bei22002-cpu/pocketvault-d14/blueprints/assets/A1-lightline-mg-blueprint.png

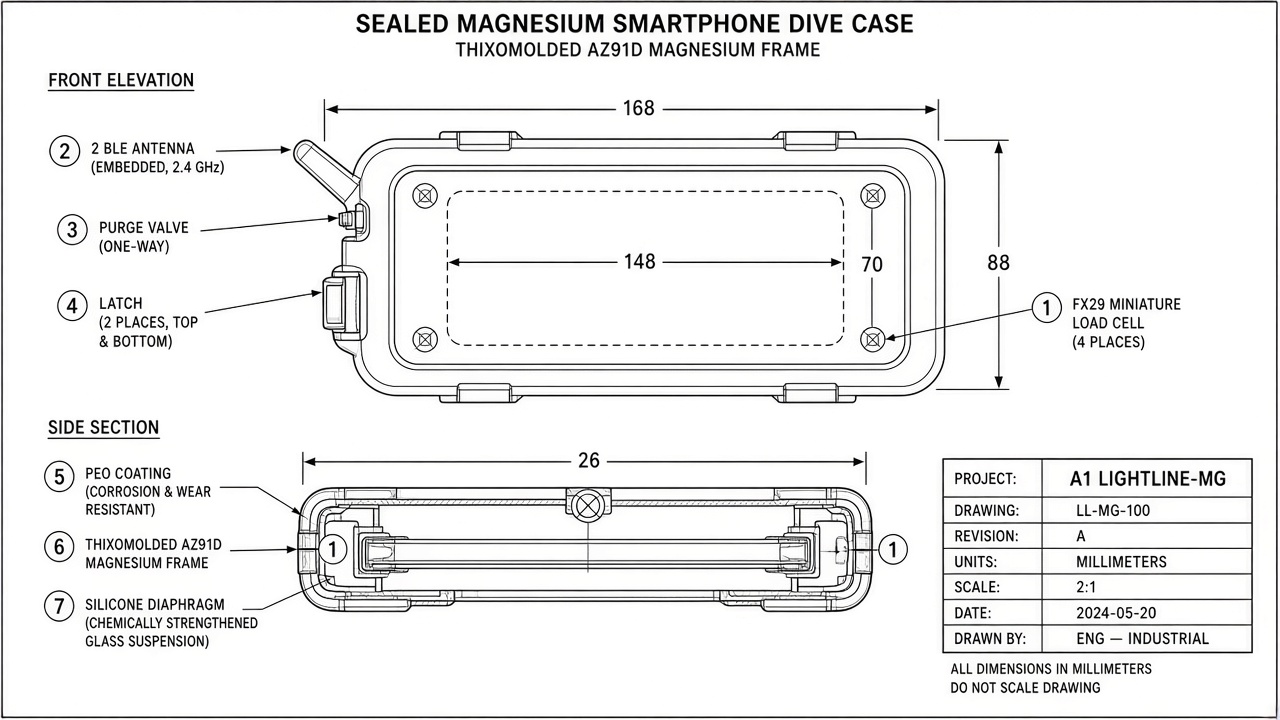
blueprints/assets/A1-lightline-mg-blueprint.png
