bei22002-cpu/pocketvault-d14/blueprints/assets/A2-carbonshell-blueprint.png

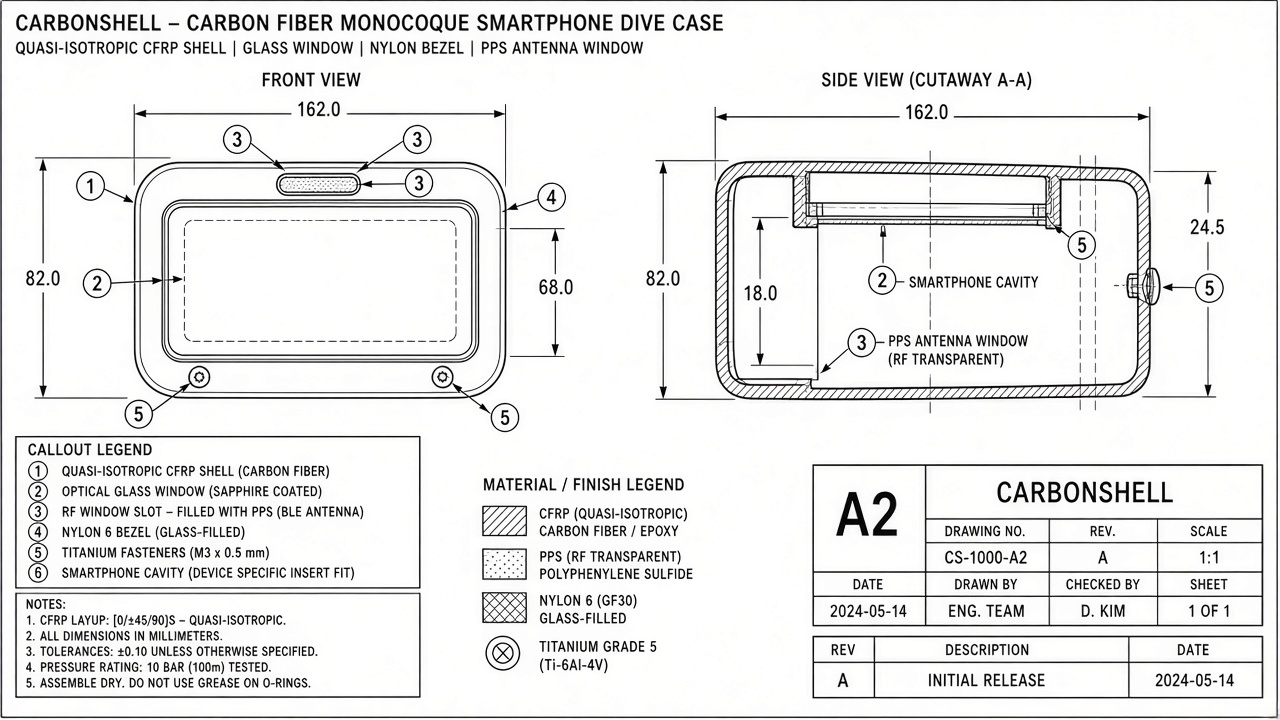
blueprints/assets/A2-carbonshell-blueprint.png
