bei22002-cpu/pocketvault-d14/blueprints/assets/A3-skeleton-blueprint.png

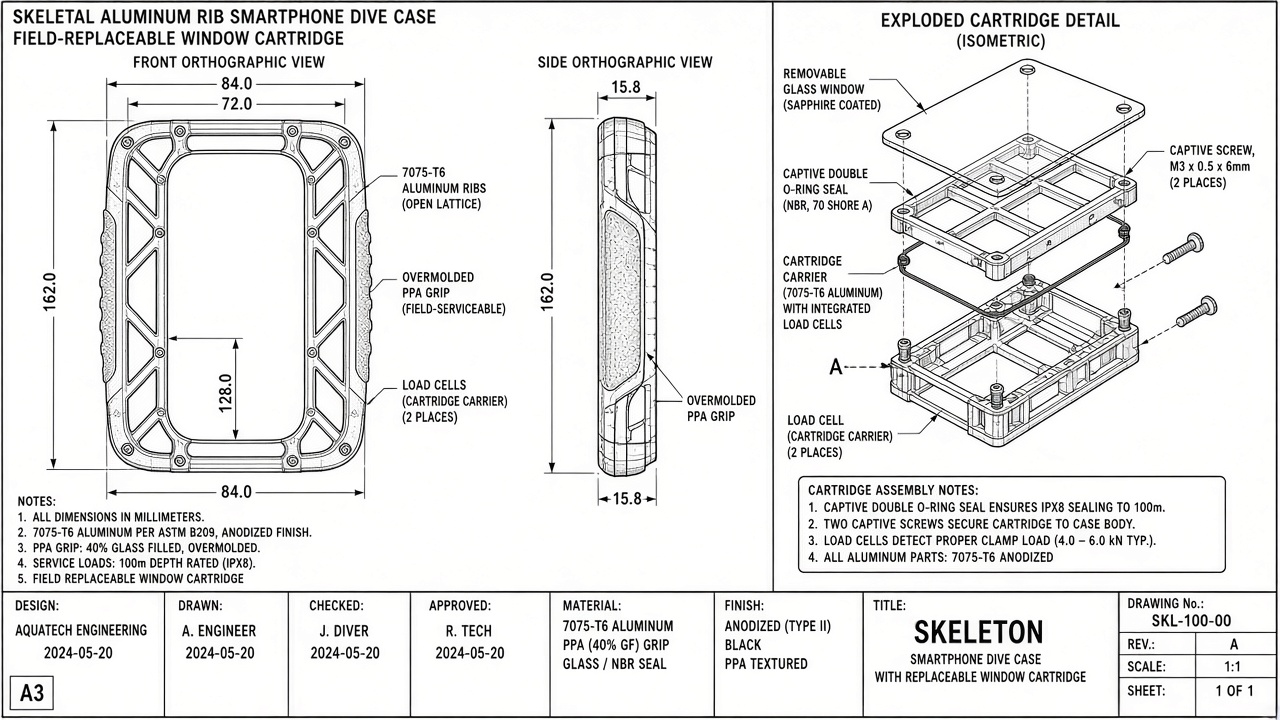
blueprints/assets/A3-skeleton-blueprint.png
