bei22002-cpu/pocketvault-d14/blueprints/assets/B5-hall-glove-blueprint.png

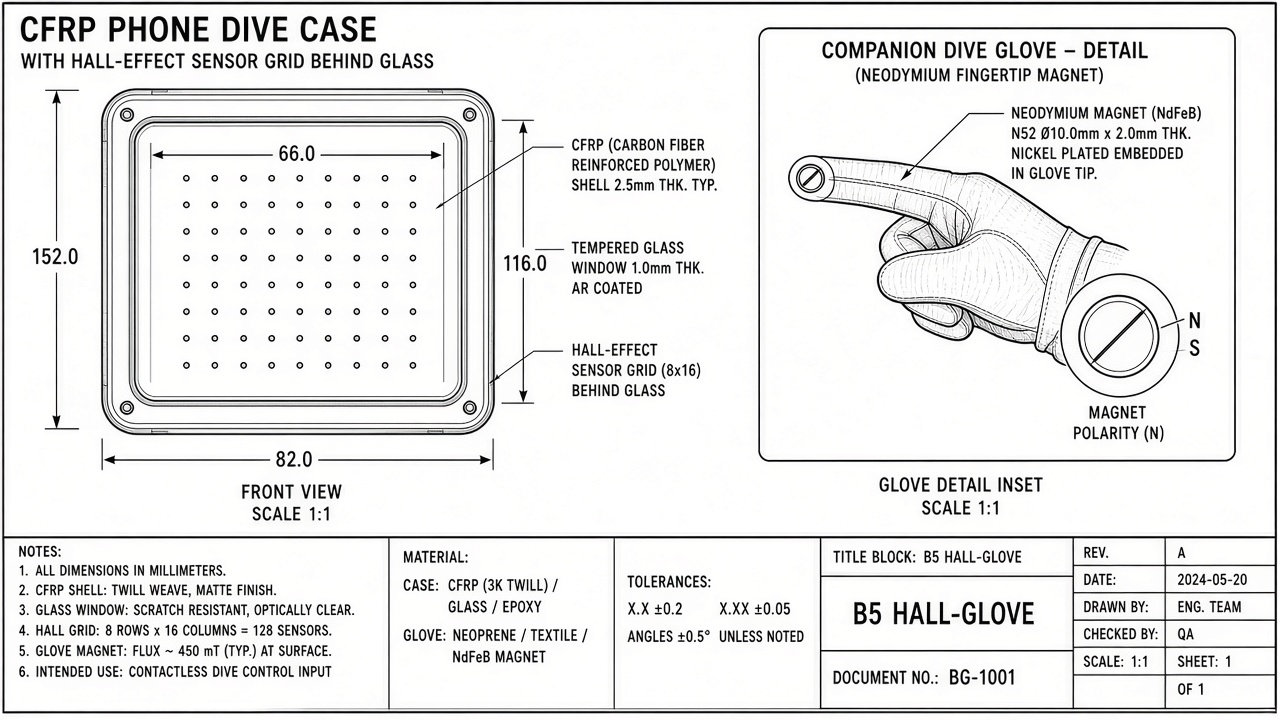
blueprints/assets/B5-hall-glove-blueprint.png
