bei22002-cpu/pocketvault-d14/blueprints/assets/B7-lamb-wave-blueprint.png

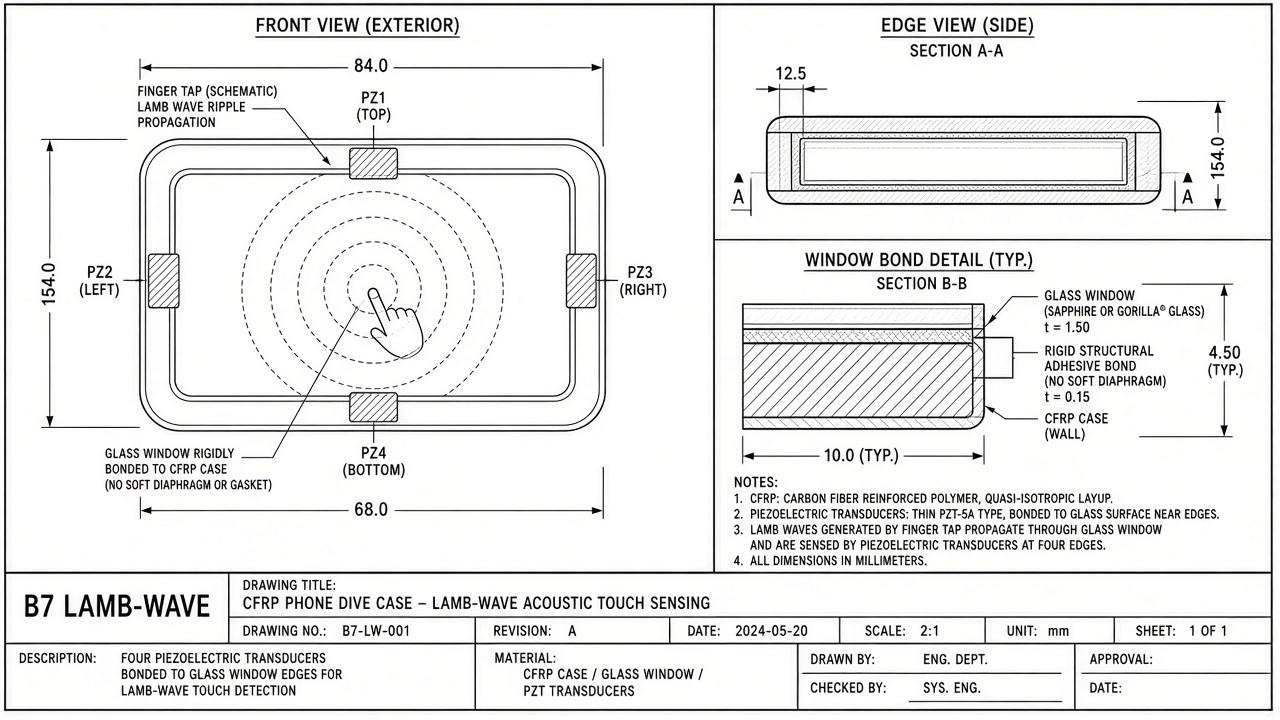
blueprints/assets/B7-lamb-wave-blueprint.png
