bei22002-cpu/pocketvault-d14/blueprints/assets/B8-resistive-hard-blueprint.png

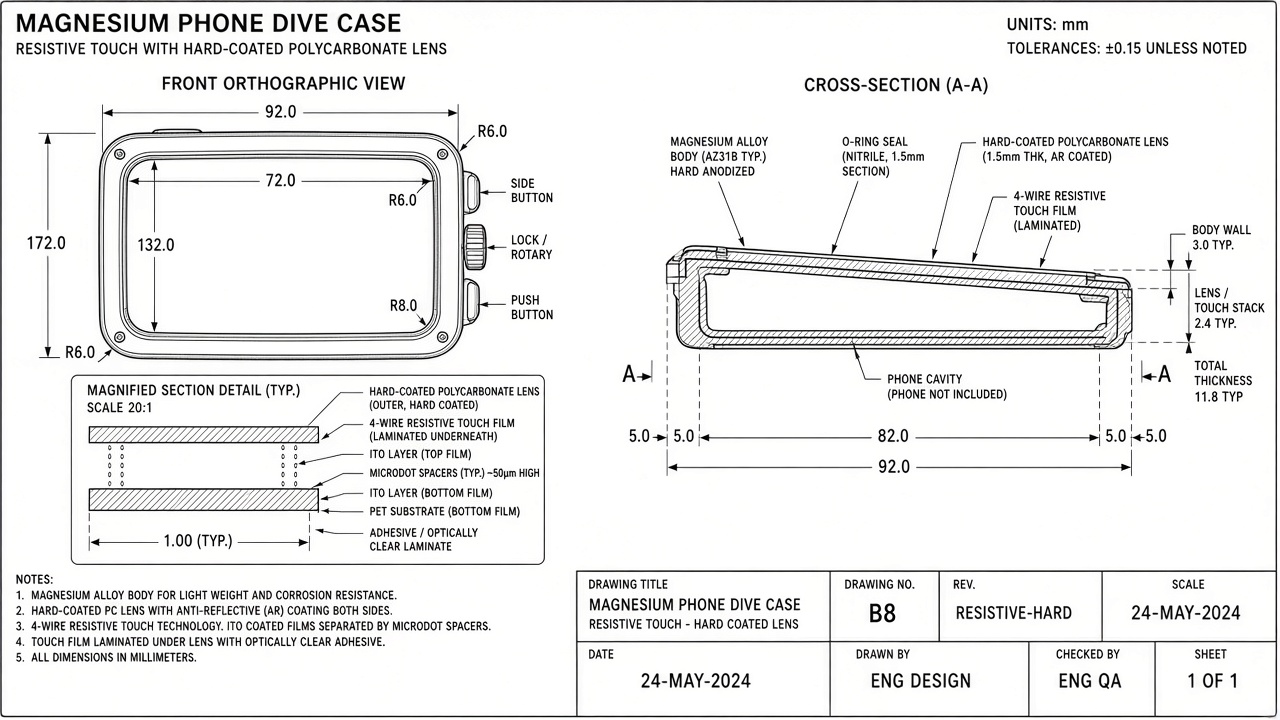
blueprints/assets/B8-resistive-hard-blueprint.png
