bei22002-cpu/pocketvault-d14/blueprints/assets/B9-gap-cap-blueprint.png

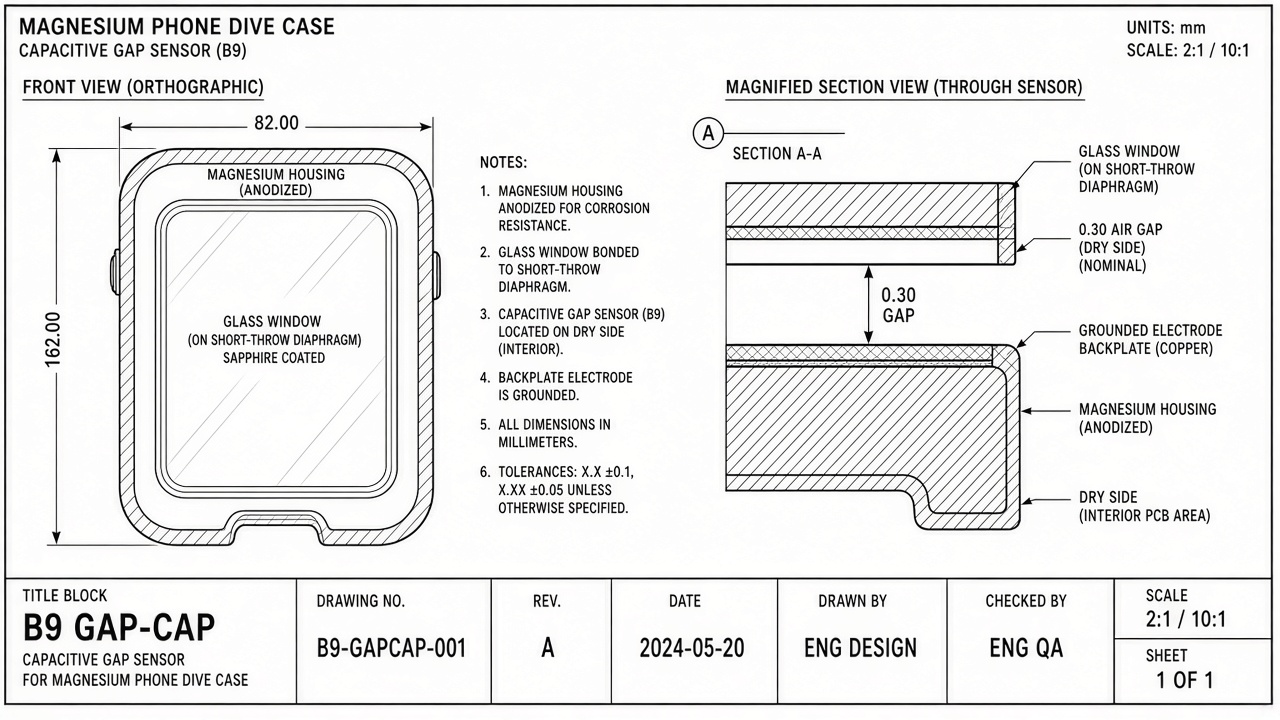
blueprints/assets/B9-gap-cap-blueprint.png
