bei22002-cpu/pocketvault-d14/blueprints/assets/C10-crownpad-blueprint.png

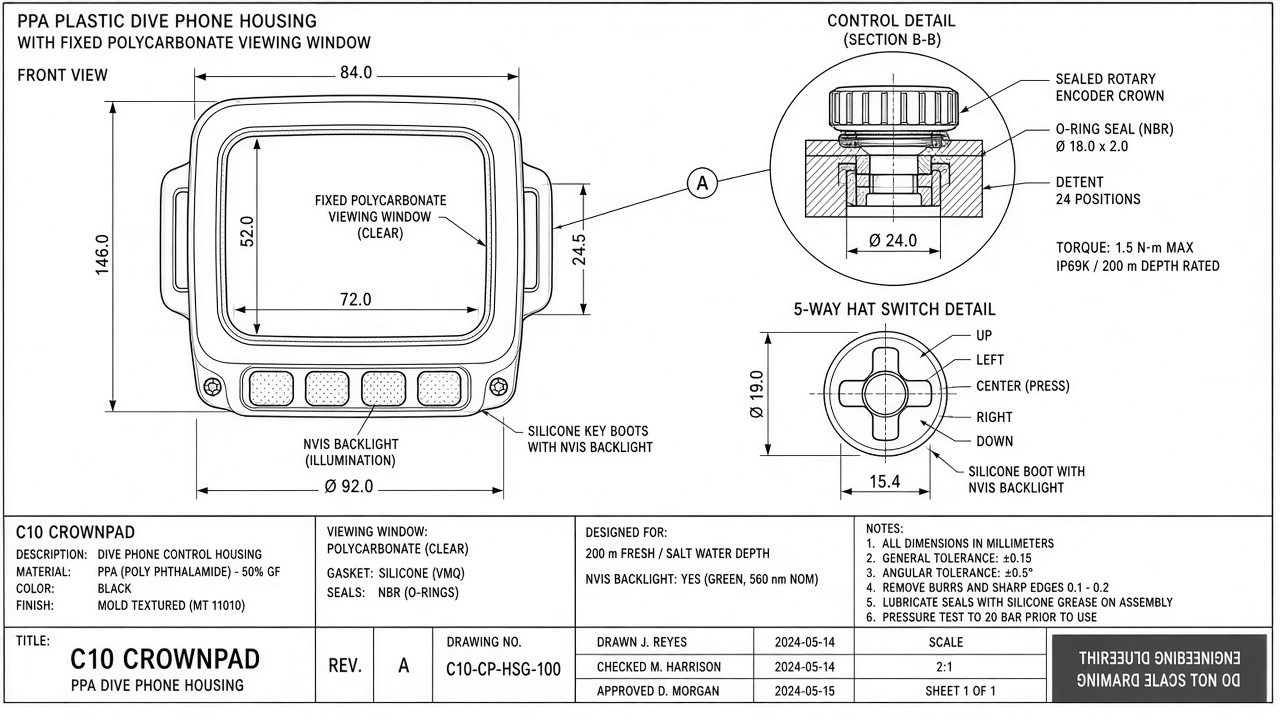
blueprints/assets/C10-crownpad-blueprint.png
