bei22002-cpu/pocketvault-d14/blueprints/assets/C11-tether-puck-blueprint.png

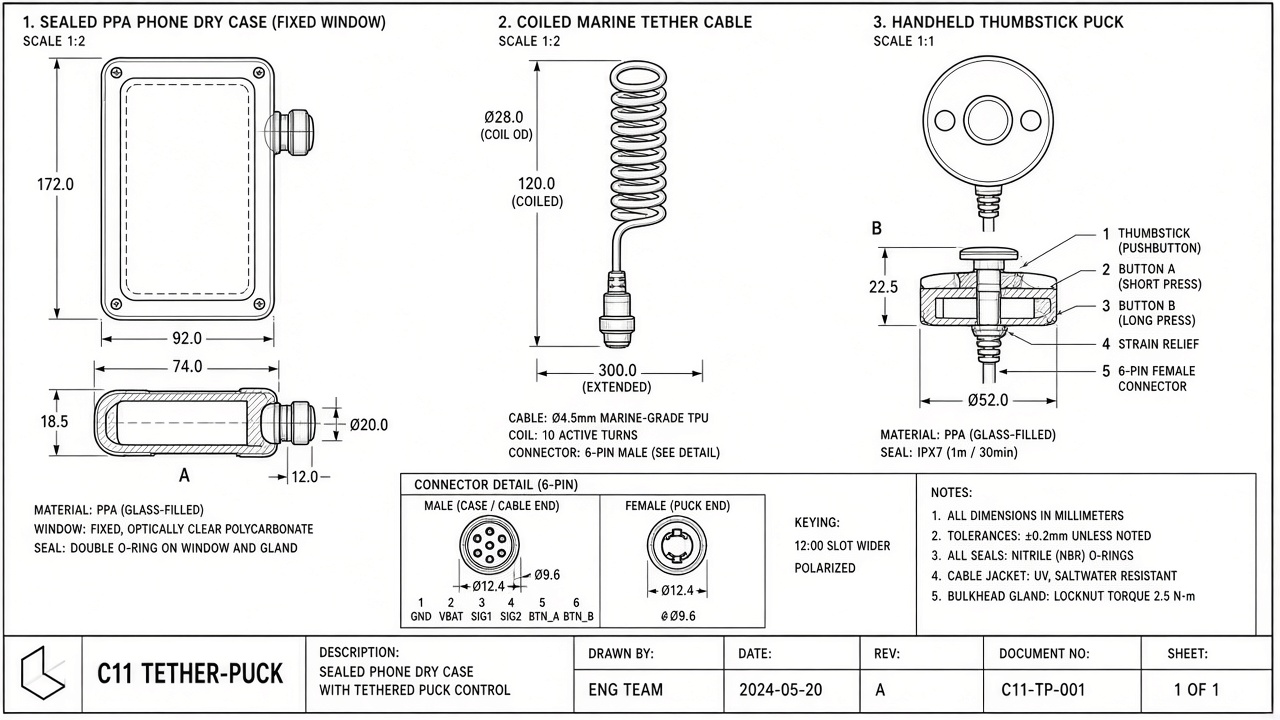
blueprints/assets/C11-tether-puck-blueprint.png
