bei22002-cpu/pocketvault-d14/blueprints/assets/C12-tilt-cursor-blueprint.png

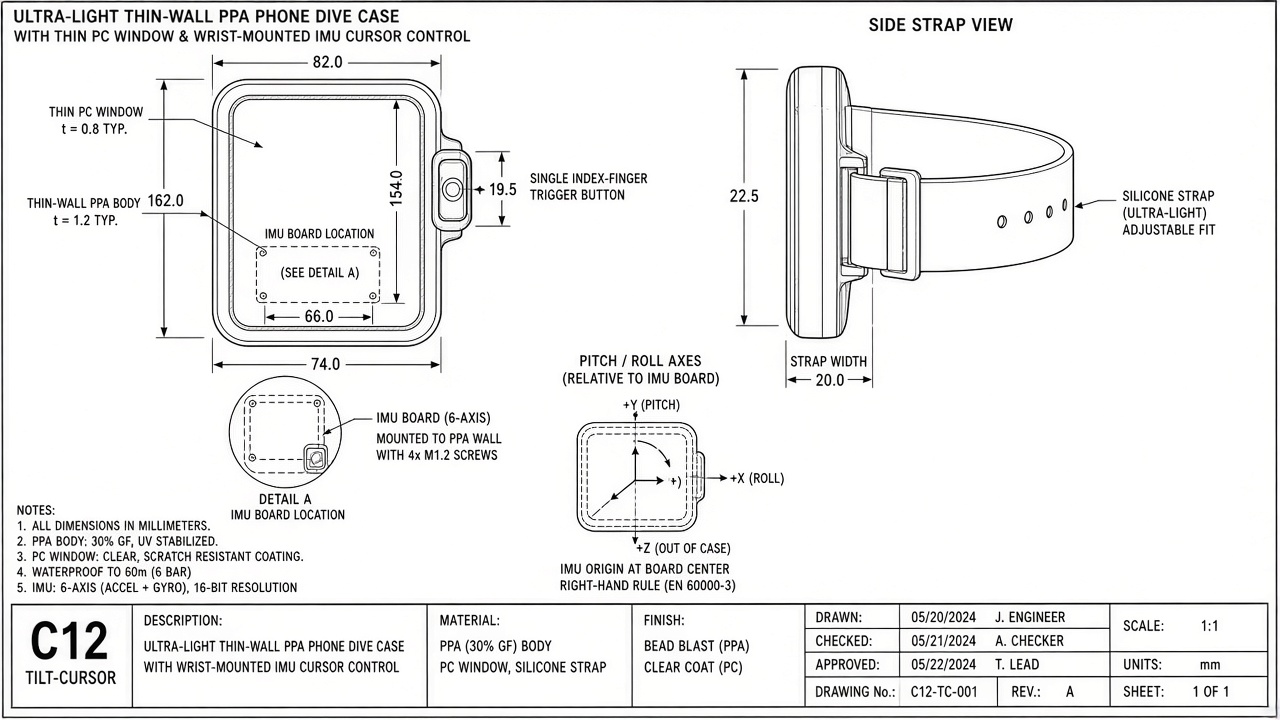
blueprints/assets/C12-tilt-cursor-blueprint.png
