bei22002-cpu/pocketvault-d14/blueprints/assets/D14-rolltop-blueprint.png

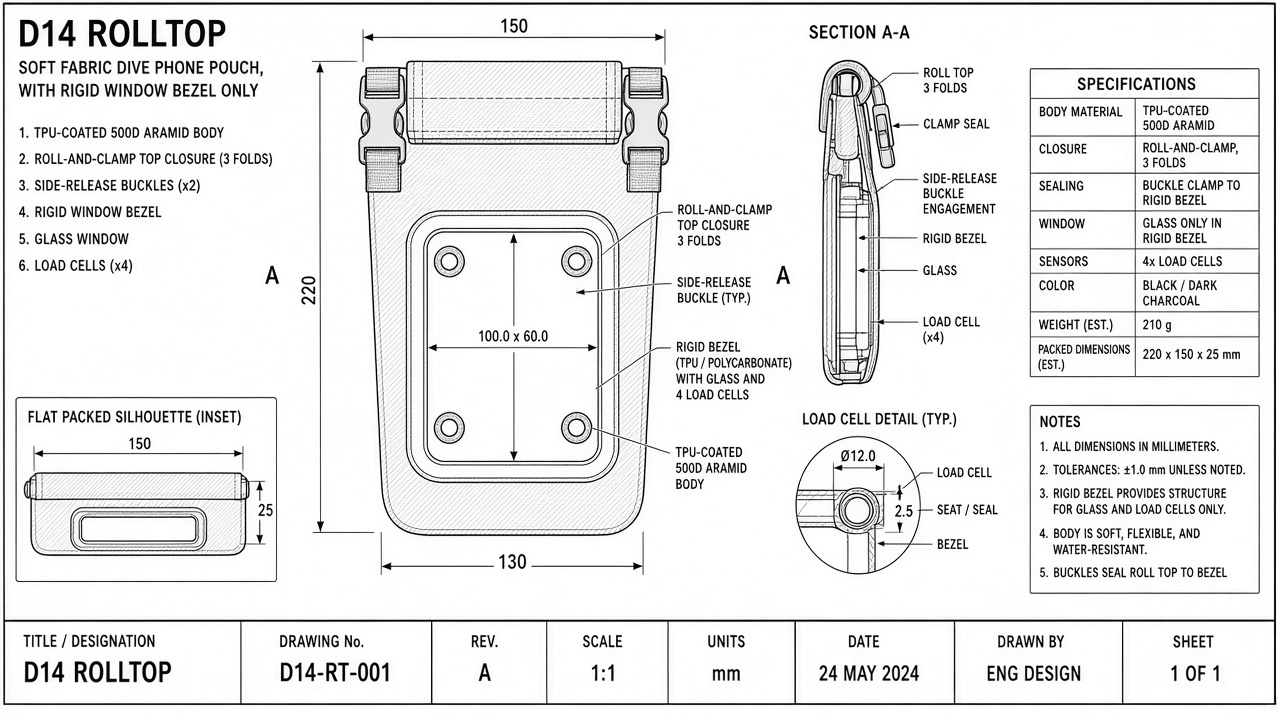
blueprints/assets/D14-rolltop-blueprint.png
