bei22002-cpu/pocketvault-d14/blueprints/assets/D15-oilfill-100-blueprint.png

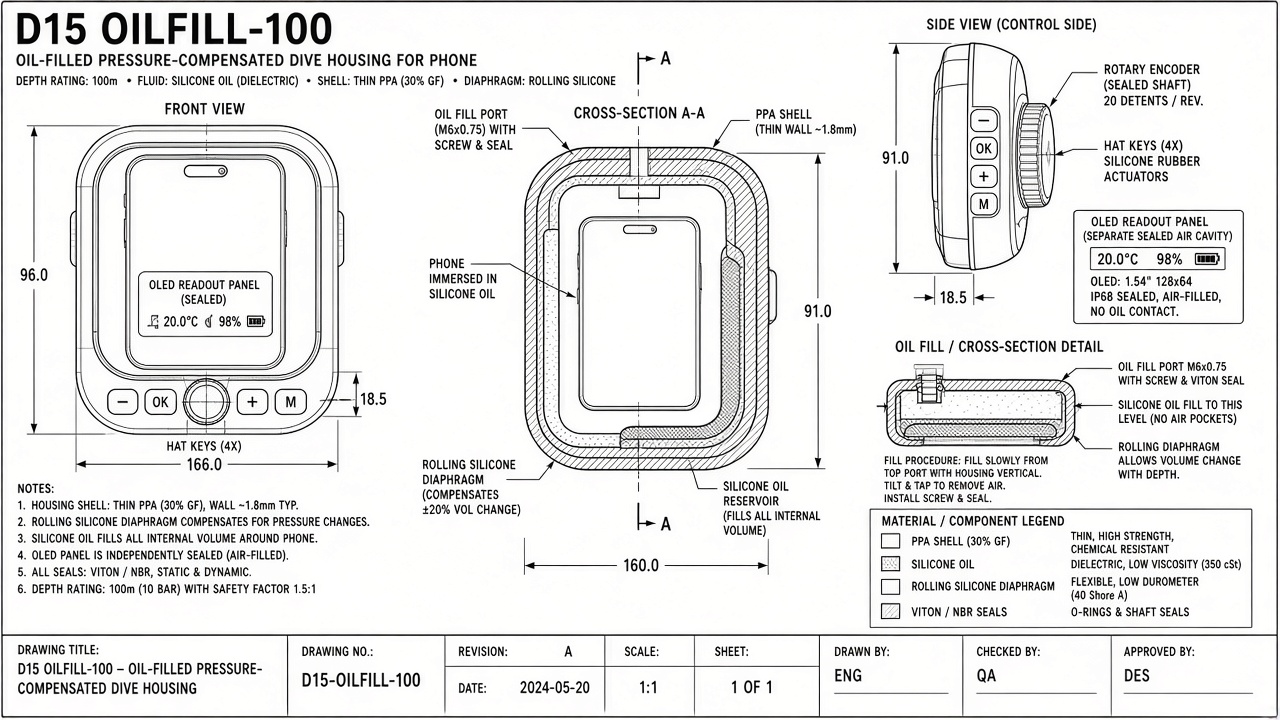
blueprints/assets/D15-oilfill-100-blueprint.png
