bei22002-cpu/pocketvault-d14/blueprints/assets/D16-floatline-blueprint.png

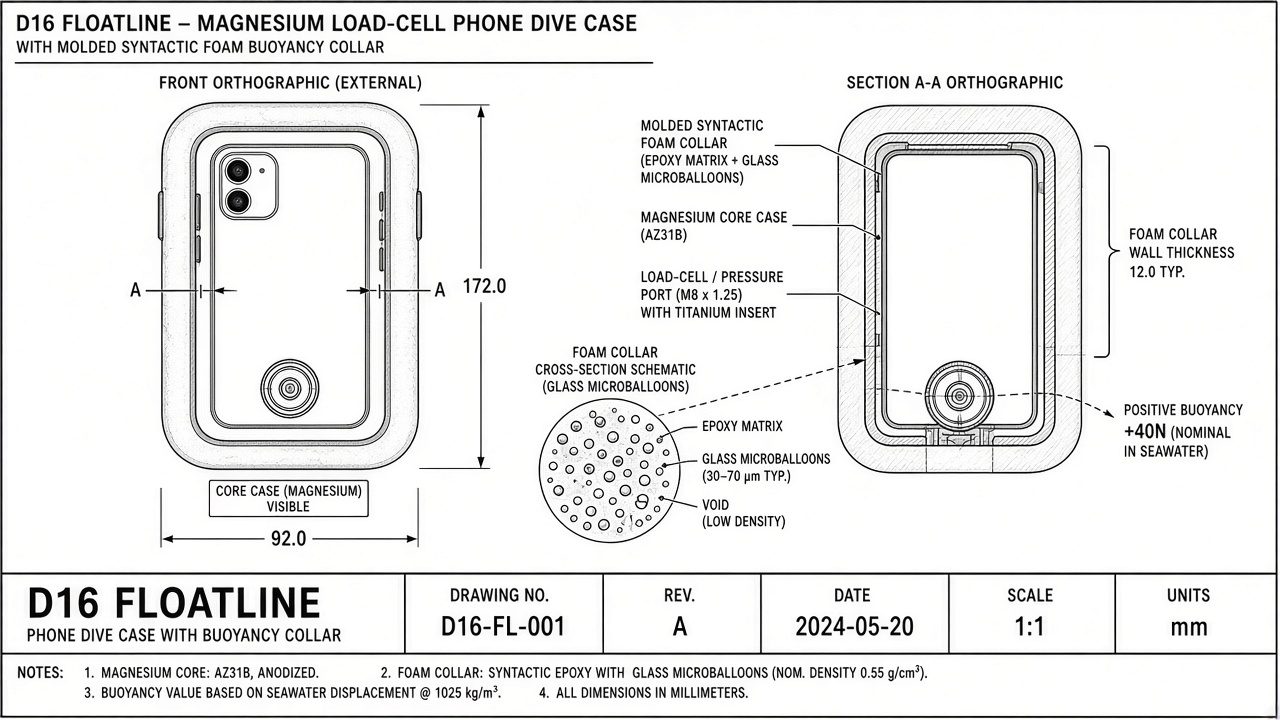
blueprints/assets/D16-floatline-blueprint.png
