bei22002-cpu/pocketvault-d14/blueprints/assets/D17-chestboard-blueprint.png

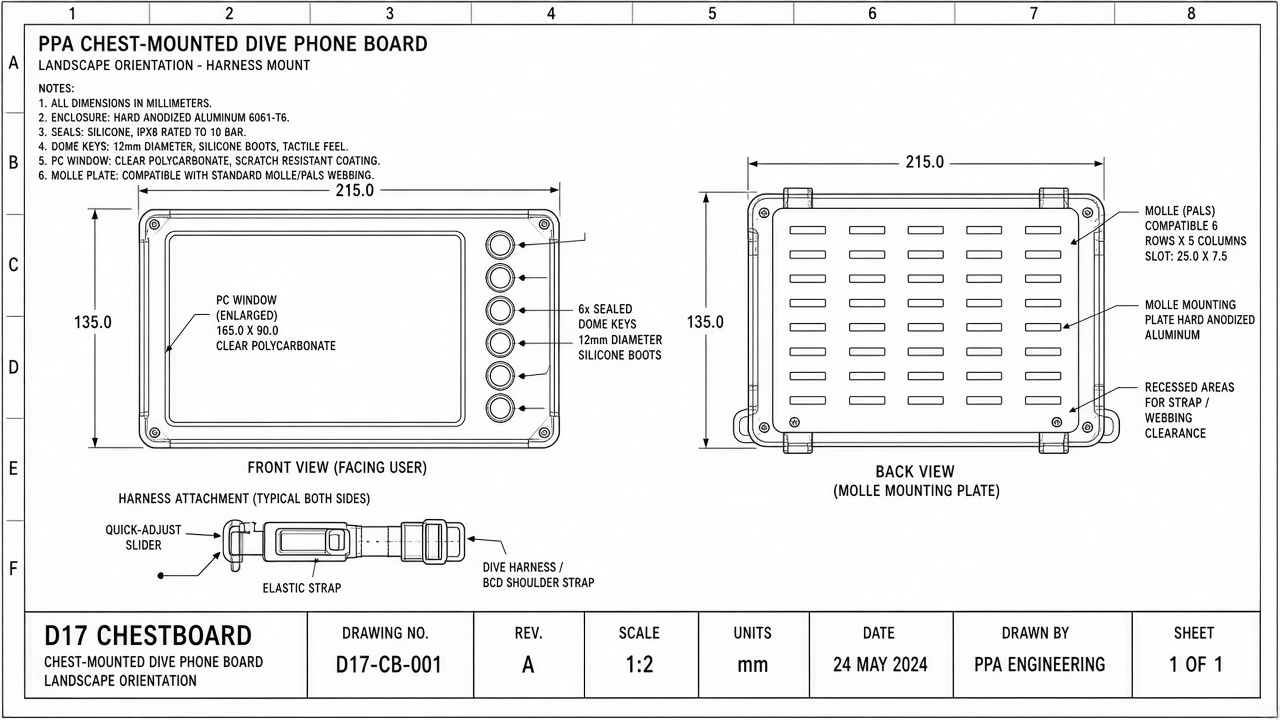
blueprints/assets/D17-chestboard-blueprint.png
