bei22002-cpu/pocketvault-d14/blueprints/assets/D18-gauntlet-blueprint.png

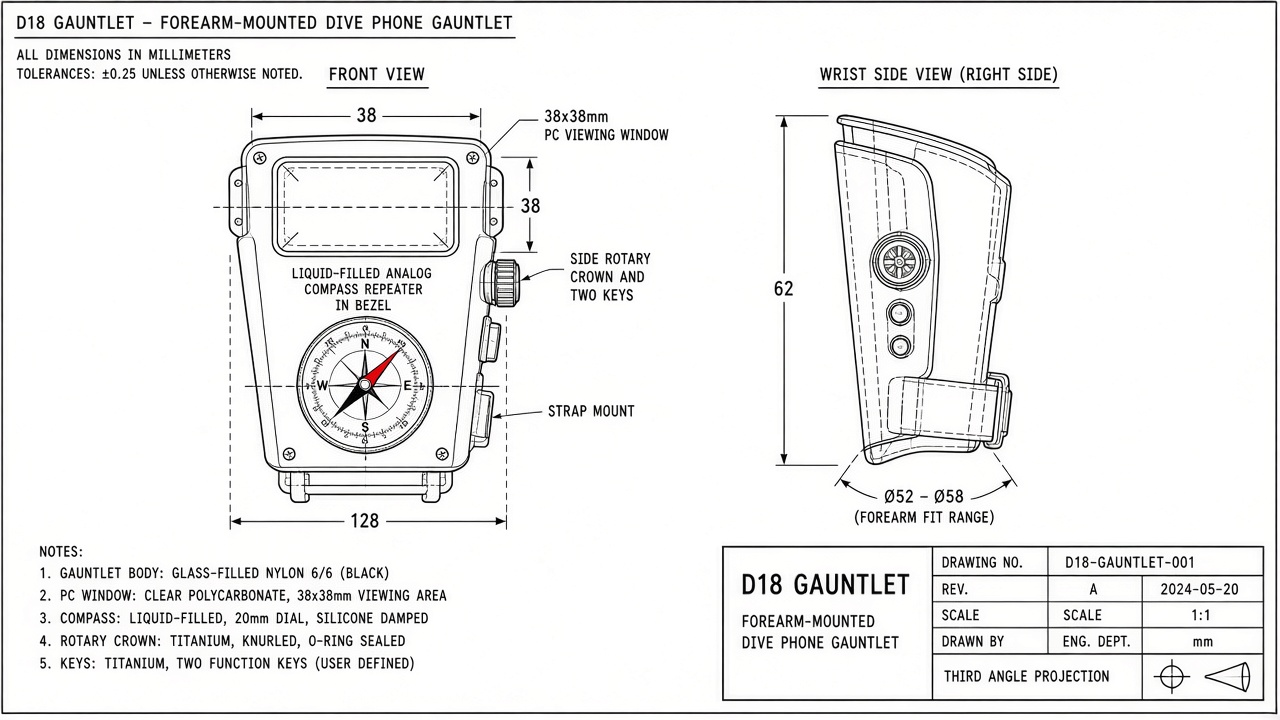
blueprints/assets/D18-gauntlet-blueprint.png
