bei22002-cpu/pocketvault-d14/blueprints/hq/hq-A2-work.png

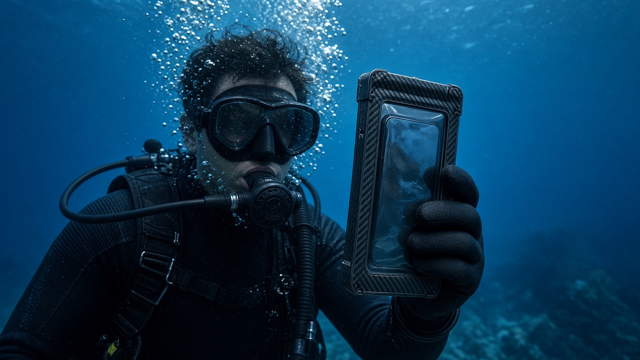
blueprints/hq/hq-A2-work.png
