bei22002-cpu/pocketvault-d14/blueprints/hq/hq-A3-explode.png

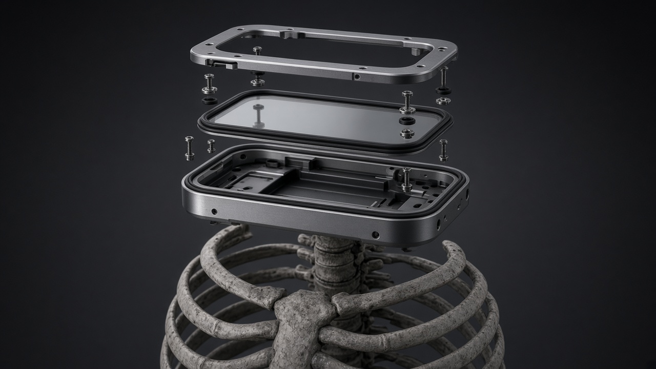
blueprints/hq/hq-A3-explode.png
