bei22002-cpu/pocketvault-d14/blueprints/hq/hq-B5-explode.png

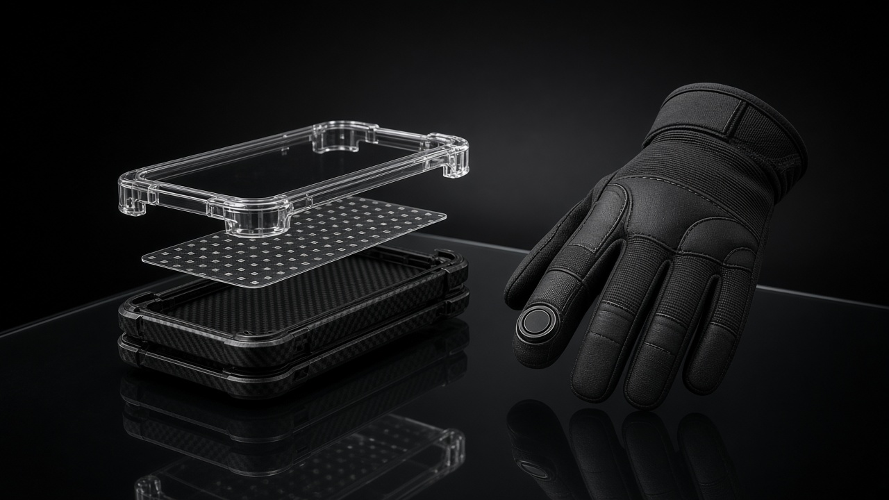
blueprints/hq/hq-B5-explode.png
