bei22002-cpu/pocketvault-d14/blueprints/hq/hq-B6-explode.png

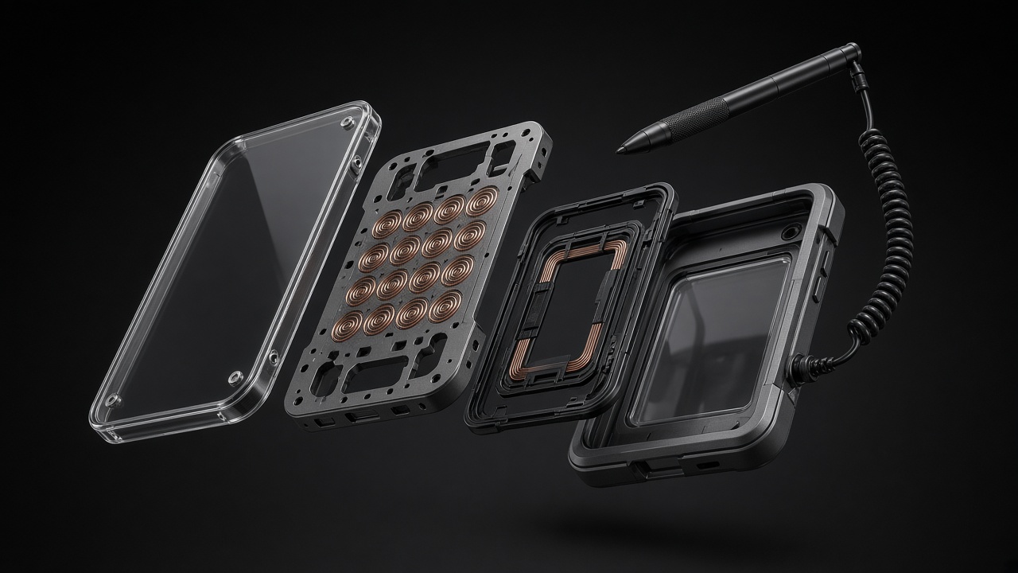
blueprints/hq/hq-B6-explode.png
