bei22002-cpu/pocketvault-d14/blueprints/hq/hq-B7-explode.png

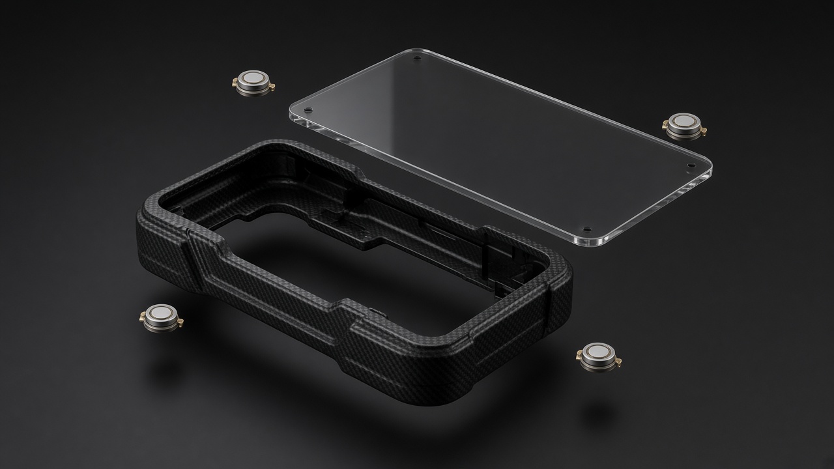
blueprints/hq/hq-B7-explode.png
