bei22002-cpu/pocketvault-d14/blueprints/hq/hq-B8-work.png

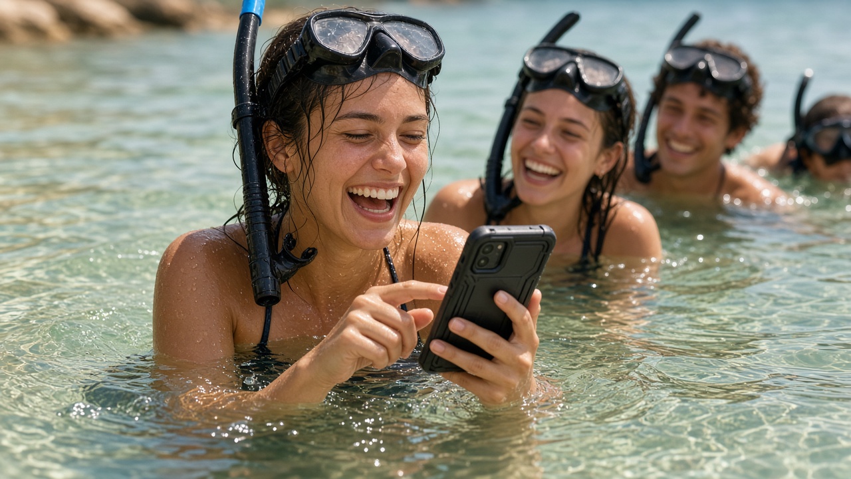
blueprints/hq/hq-B8-work.png
