bei22002-cpu/pocketvault-d14/blueprints/hq/hq-C10-work.png

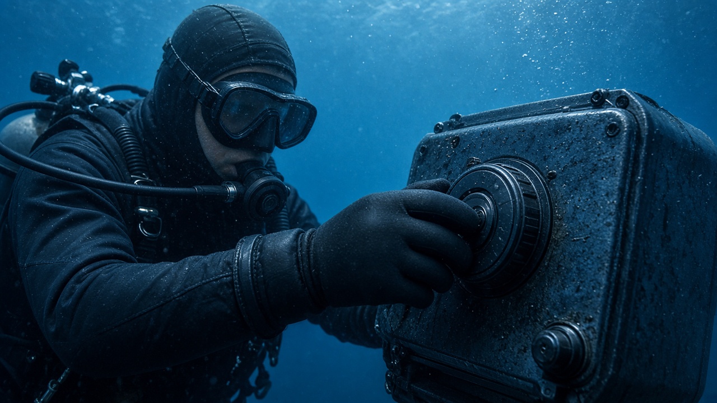
blueprints/hq/hq-C10-work.png
