bei22002-cpu/pocketvault-d14/blueprints/hq/hq-C11-explode.png

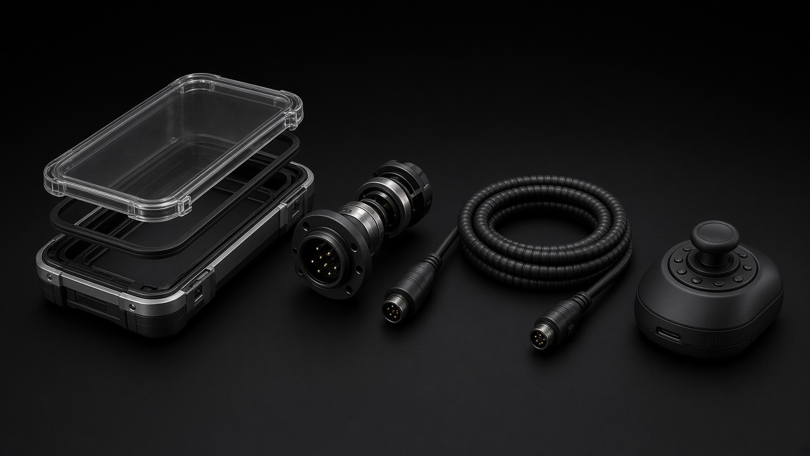
blueprints/hq/hq-C11-explode.png
