bei22002-cpu/pocketvault-d14/blueprints/hq/hq-C12-explode.png

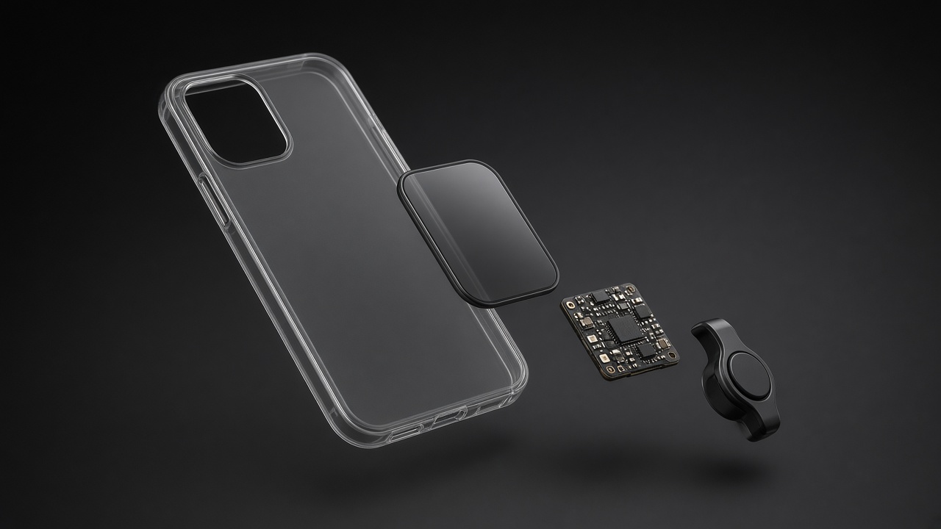
blueprints/hq/hq-C12-explode.png
