bei22002-cpu/pocketvault-d14/blueprints/hq/hq-C13-work.png

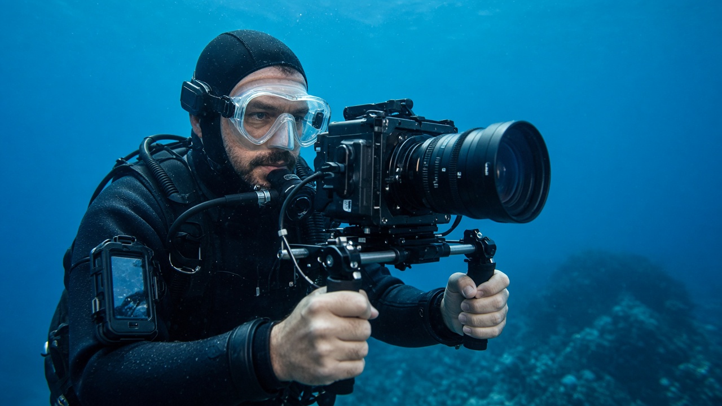
blueprints/hq/hq-C13-work.png
