bei22002-cpu/pocketvault-d14/blueprints/hq/hq-D14-explode.png

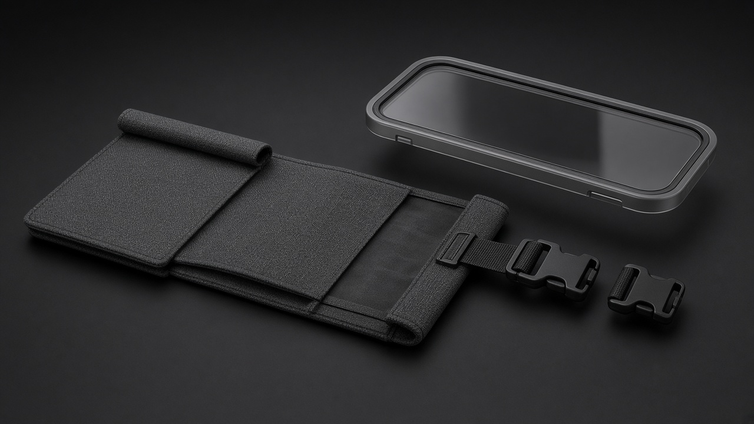
blueprints/hq/hq-D14-explode.png
