bei22002-cpu/pocketvault-d14/blueprints/hq/hq-D14-work.png

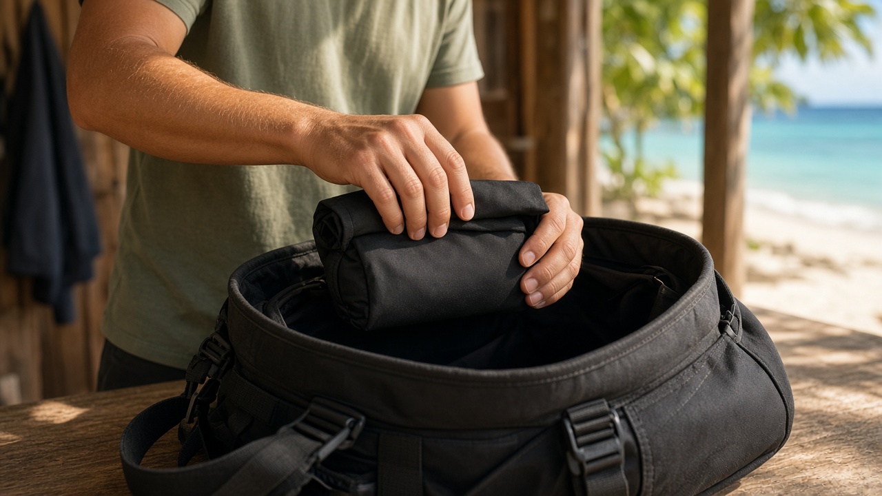
blueprints/hq/hq-D14-work.png
