bei22002-cpu/pocketvault-d14/blueprints/hq/hq-D15-explode.png

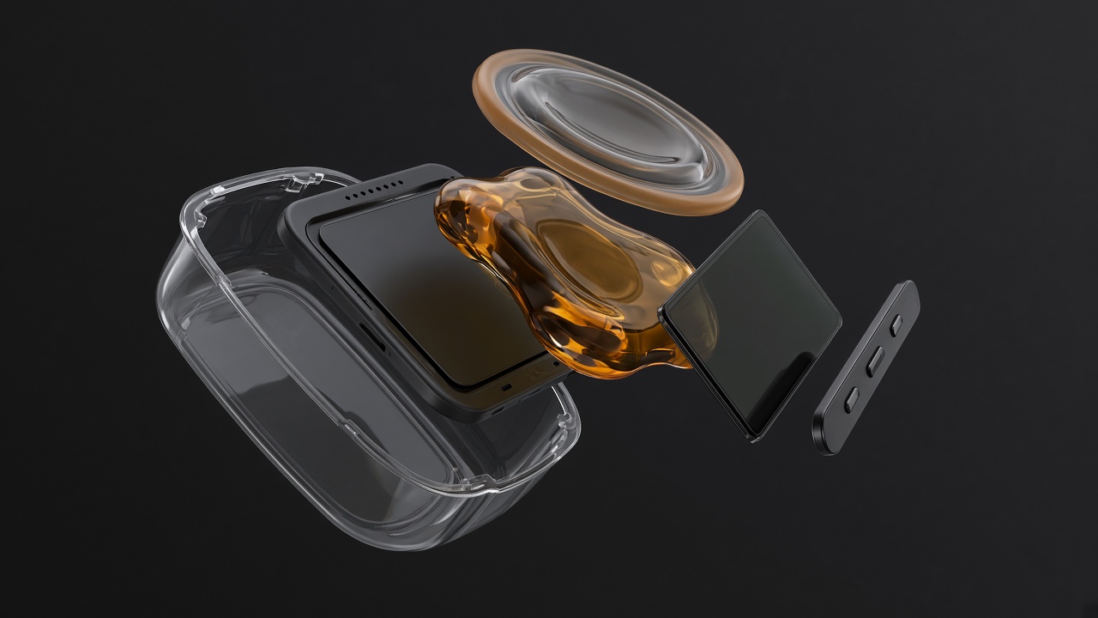
blueprints/hq/hq-D15-explode.png
