bei22002-cpu/pocketvault-d14/blueprints/hq/hq-D16-explode.png

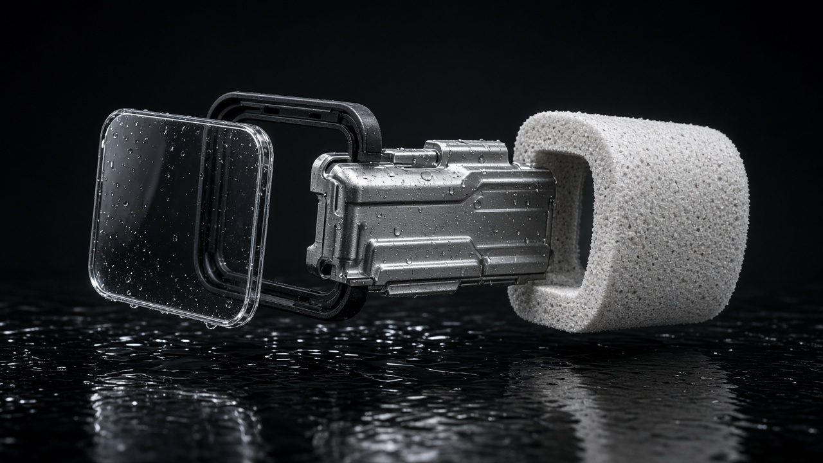
blueprints/hq/hq-D16-explode.png
