bei22002-cpu/pocketvault-d14/blueprints/hq/hq-D17-explode.png

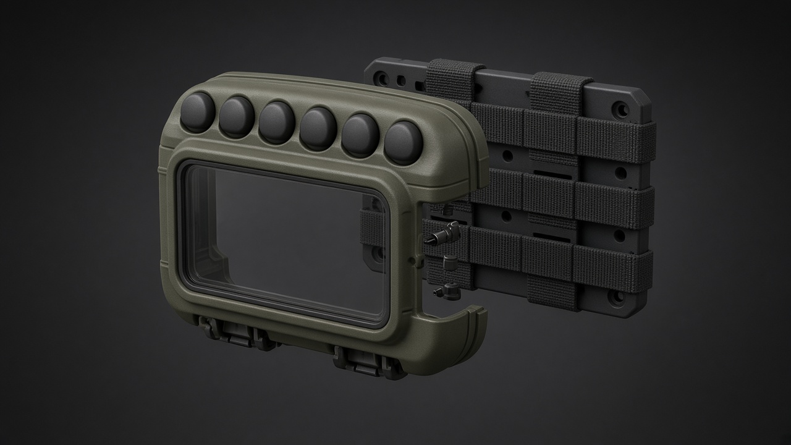
blueprints/hq/hq-D17-explode.png
