bei22002-cpu/pocketvault-d14/blueprints/hq/hq-D17-work.png

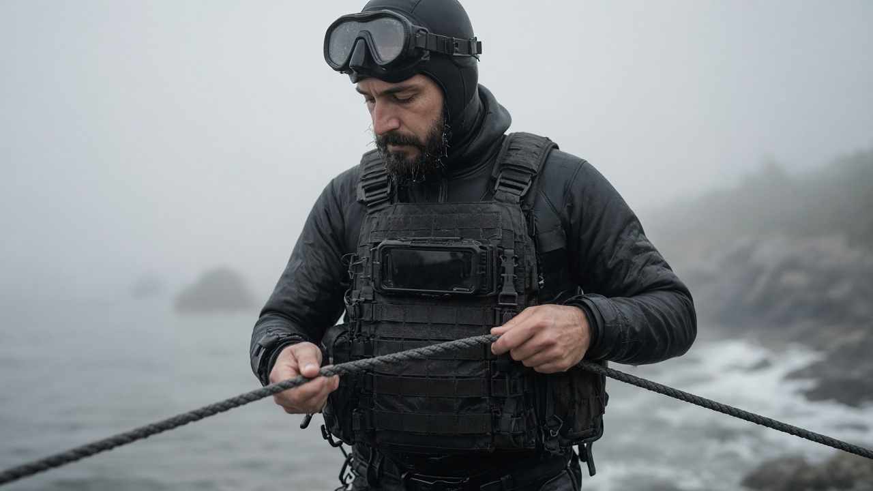
blueprints/hq/hq-D17-work.png
