bei22002-cpu/pocketvault-d14/blueprints/lifestyle/life-A1-lightline-mg.png

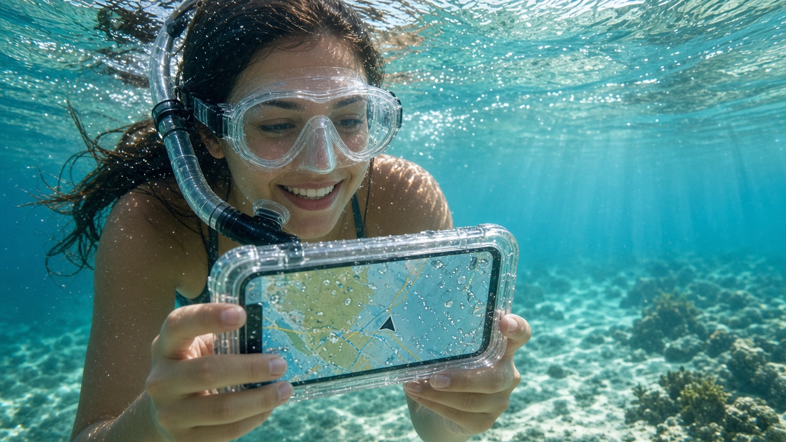
blueprints/lifestyle/life-A1-lightline-mg.png
