bei22002-cpu/pocketvault-d14/blueprints/lifestyle/life-A2-carbonshell.png

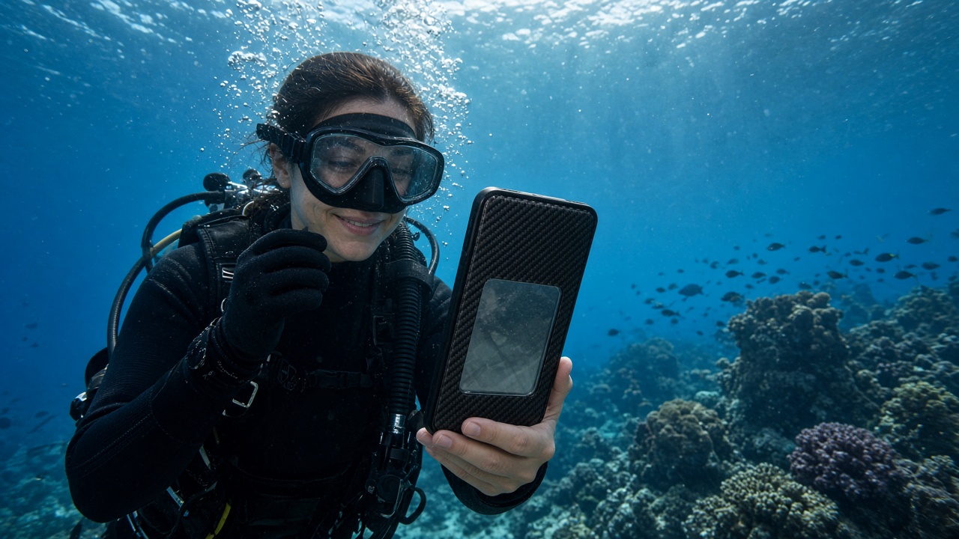
blueprints/lifestyle/life-A2-carbonshell.png
