bei22002-cpu/pocketvault-d14/blueprints/lifestyle/life-A3-skeleton.png

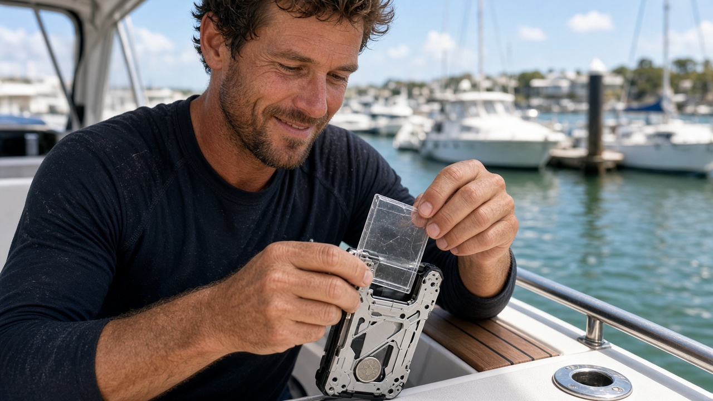
blueprints/lifestyle/life-A3-skeleton.png
