bei22002-cpu/pocketvault-d14/blueprints/lifestyle/life-A4-titan-20.png

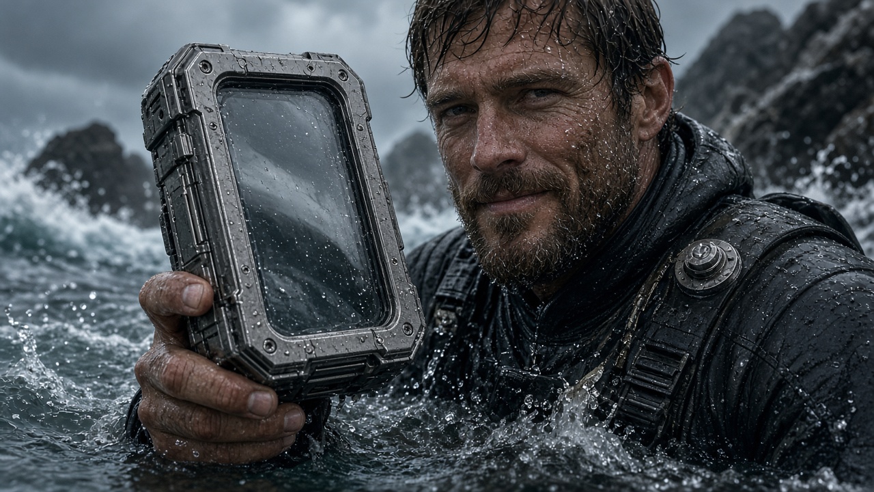
blueprints/lifestyle/life-A4-titan-20.png
