bei22002-cpu/pocketvault-d14/blueprints/lifestyle/life-B5-hall-glove.png

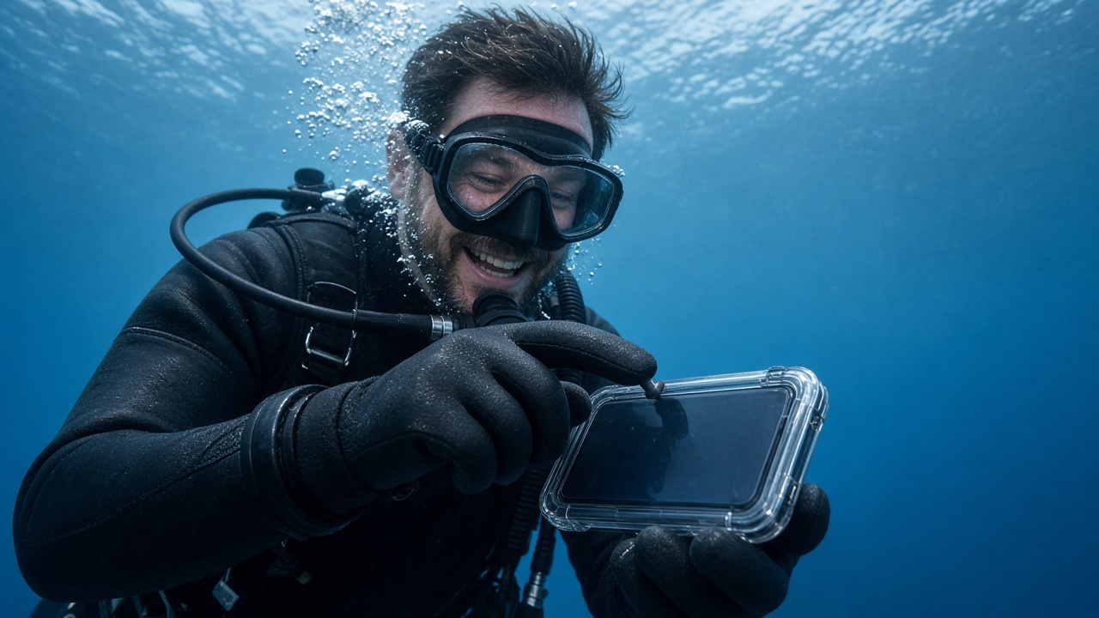
blueprints/lifestyle/life-B5-hall-glove.png
