bei22002-cpu/pocketvault-d14/blueprints/lifestyle/life-B6-stylus-emr.png

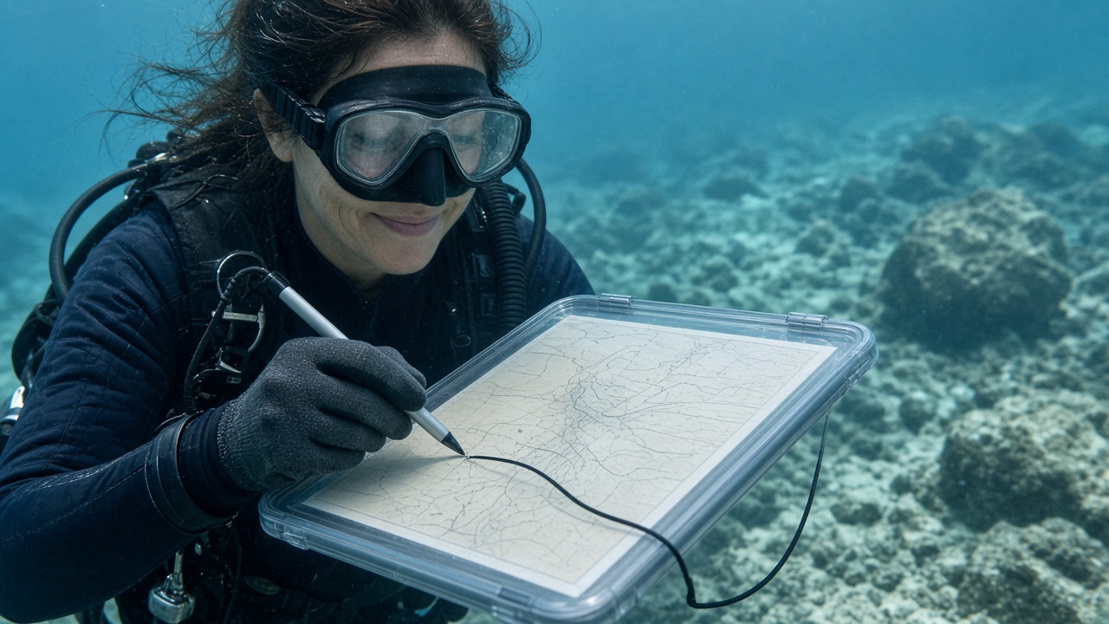
blueprints/lifestyle/life-B6-stylus-emr.png
