bei22002-cpu/pocketvault-d14/blueprints/lifestyle/life-B7-lamb-wave.png

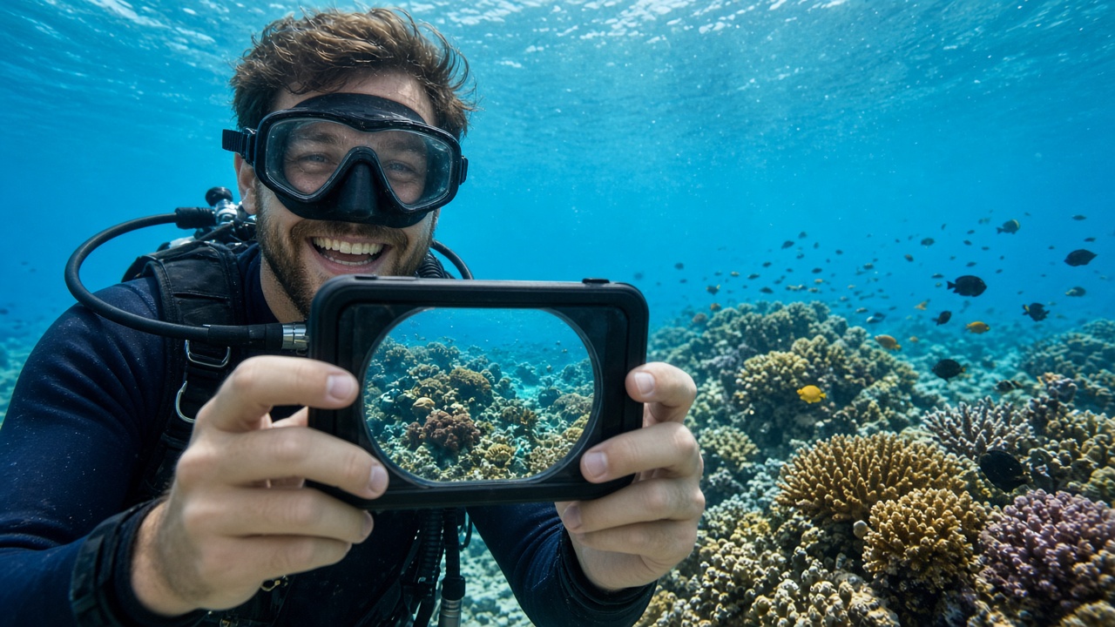
blueprints/lifestyle/life-B7-lamb-wave.png
