bei22002-cpu/pocketvault-d14/blueprints/lifestyle/life-B8-resistive-hard.png

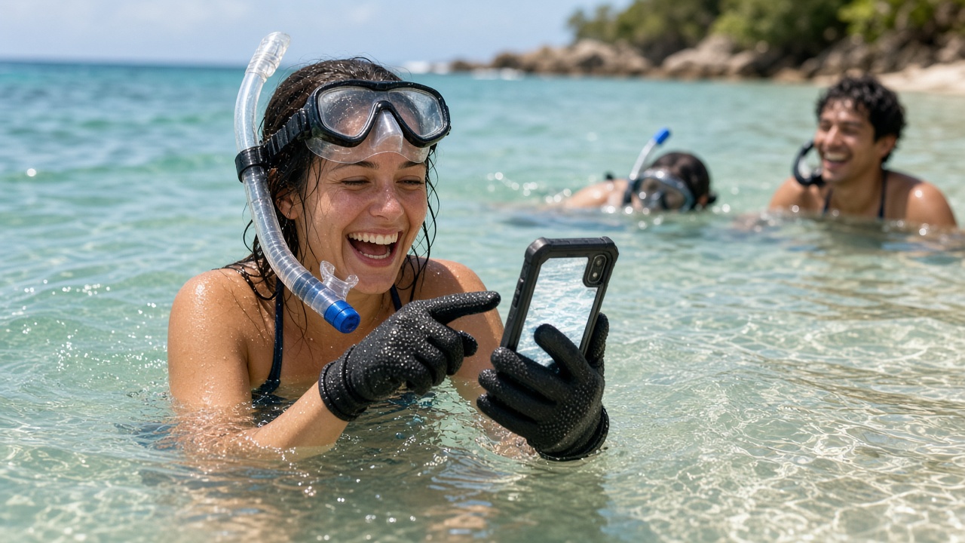
blueprints/lifestyle/life-B8-resistive-hard.png
