bei22002-cpu/pocketvault-d14/blueprints/lifestyle/life-B9-gap-cap.png

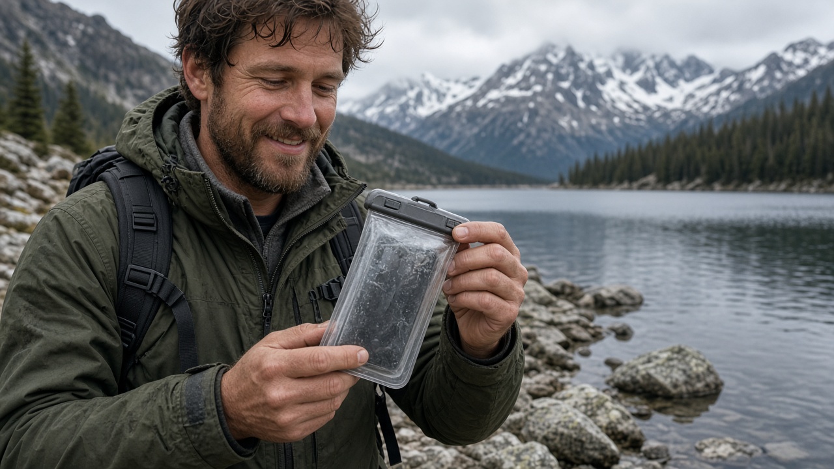
blueprints/lifestyle/life-B9-gap-cap.png
