bei22002-cpu/pocketvault-d14/blueprints/lifestyle/life-C10-crownpad.png

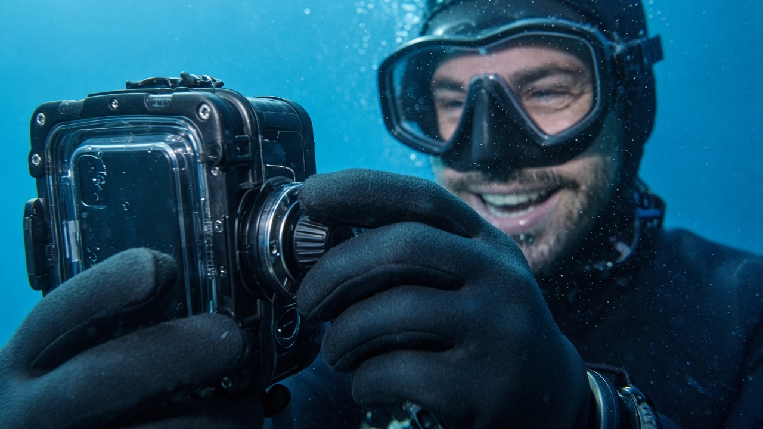
blueprints/lifestyle/life-C10-crownpad.png
