bei22002-cpu/pocketvault-d14/blueprints/lifestyle/life-C11-tether-puck.png

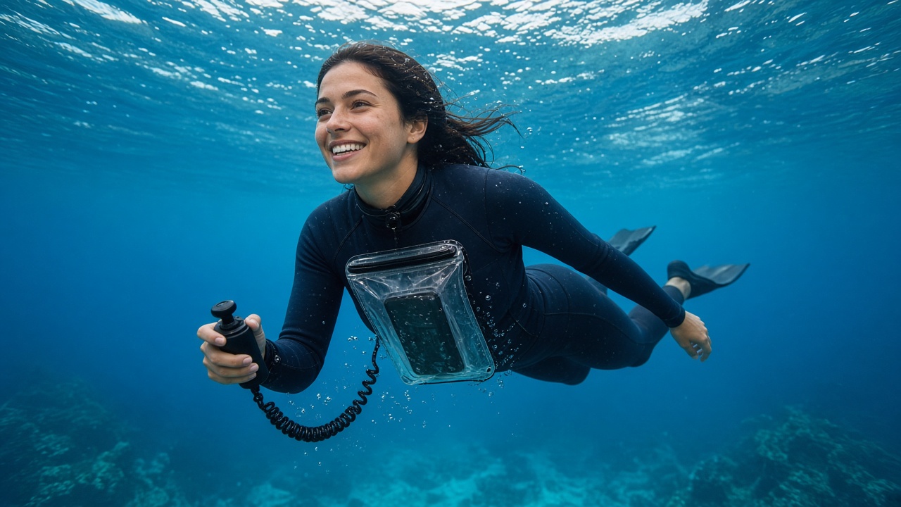
blueprints/lifestyle/life-C11-tether-puck.png
