bei22002-cpu/pocketvault-d14/blueprints/lifestyle/life-C12-tilt-cursor.png

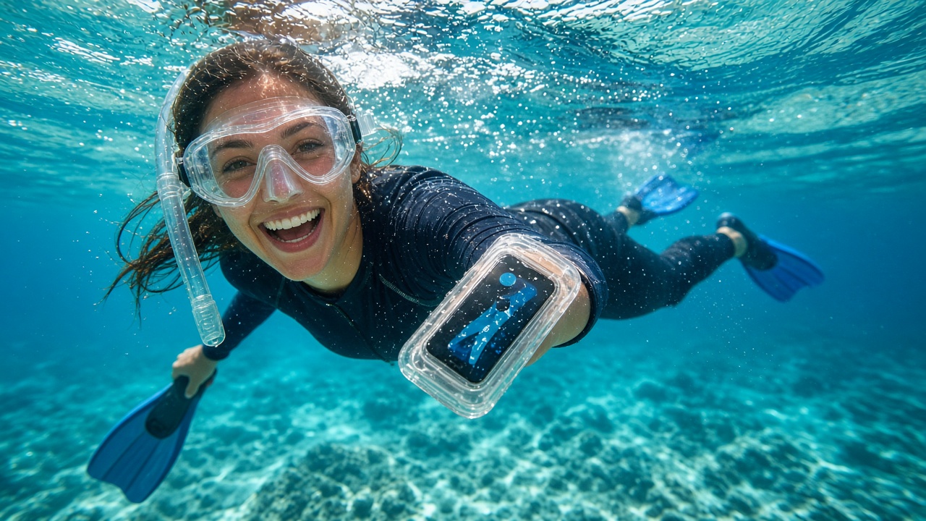
blueprints/lifestyle/life-C12-tilt-cursor.png
