bei22002-cpu/pocketvault-d14/blueprints/lifestyle/life-C13-voice-ptt.png

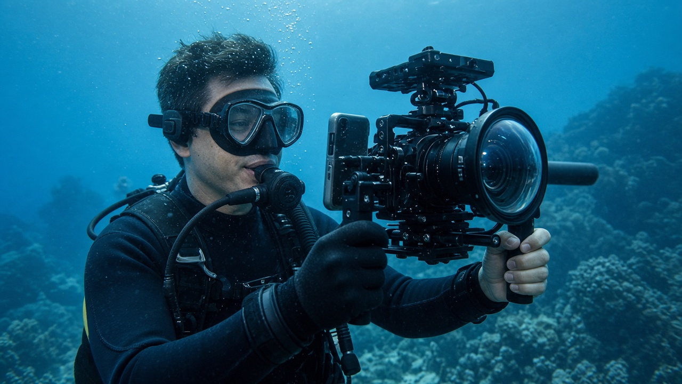
blueprints/lifestyle/life-C13-voice-ptt.png
