bei22002-cpu/pocketvault-d14/blueprints/lifestyle/life-D14-rolltop.png

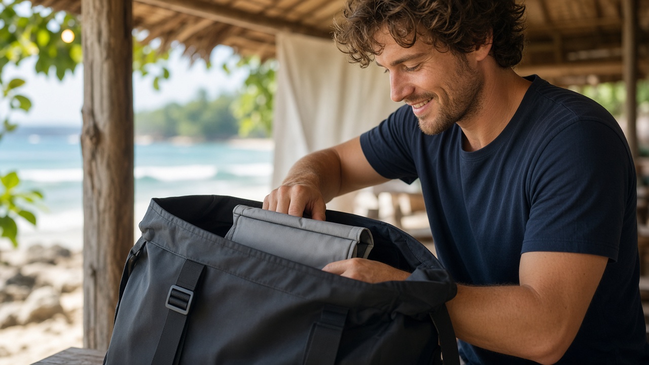
blueprints/lifestyle/life-D14-rolltop.png
