bei22002-cpu/pocketvault-d14/blueprints/lifestyle/life-D15-oilfill-100.png

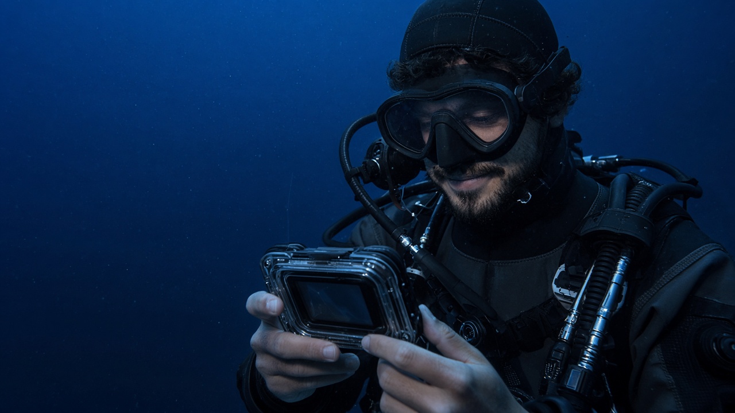
blueprints/lifestyle/life-D15-oilfill-100.png
