bei22002-cpu/pocketvault-d14/blueprints/lifestyle/life-D16-floatline.png

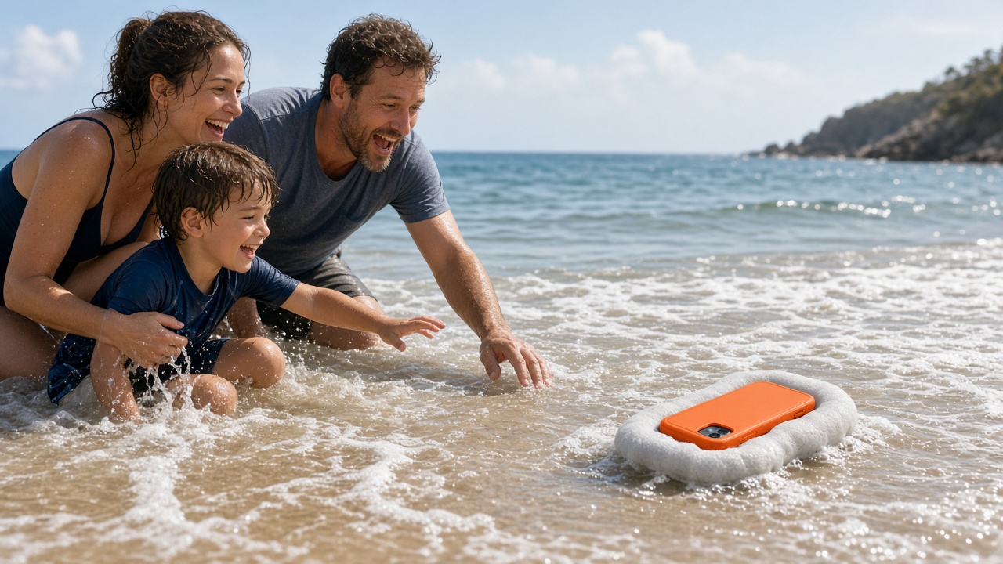
blueprints/lifestyle/life-D16-floatline.png
