bei22002-cpu/pocketvault-d14/blueprints/lifestyle/life-D17-chestboard.png

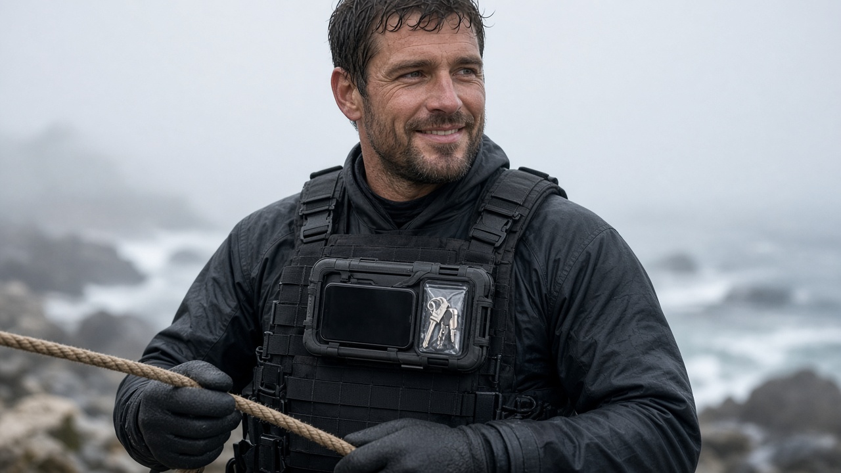
blueprints/lifestyle/life-D17-chestboard.png
