bei22002-cpu/pocketvault-d14/blueprints/lifestyle/life-D18-gauntlet.png

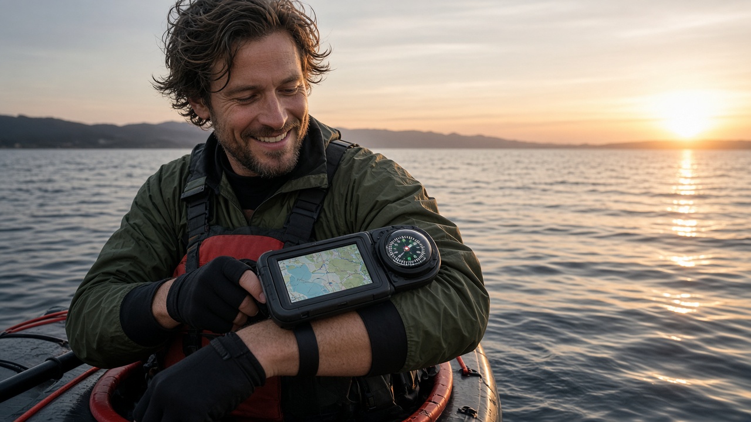
blueprints/lifestyle/life-D18-gauntlet.png
