bei22002-cpu/pocketvault-d14/blueprints/pitch/clamp-macro.png

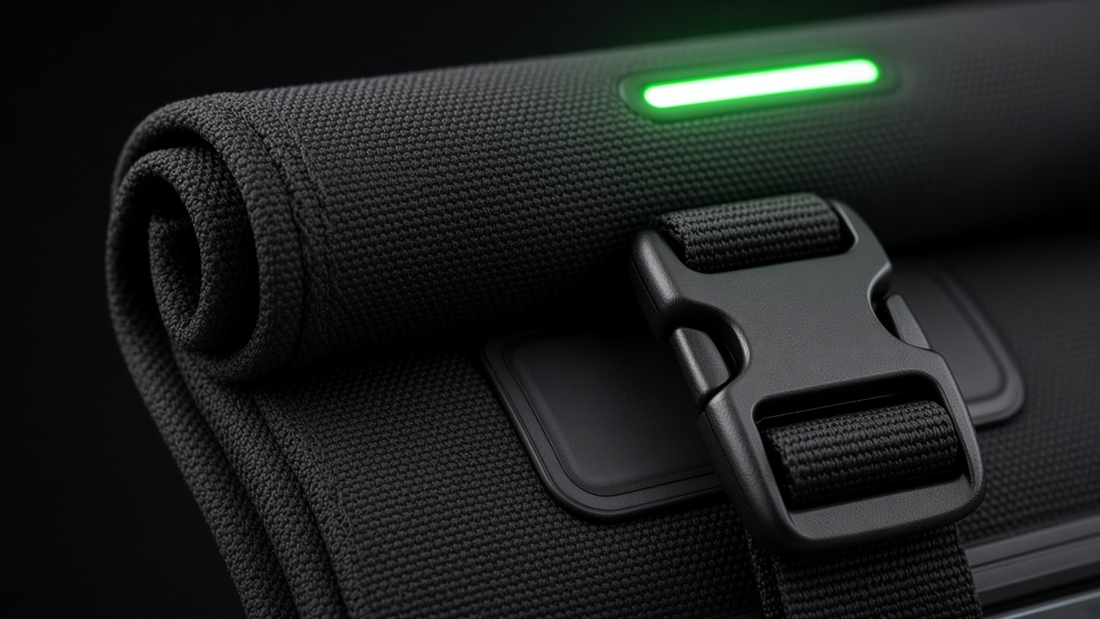
blueprints/pitch/clamp-macro.png
