bei22002-cpu/pocketvault-d14/blueprints/pitch/in-use-underwater.jpg

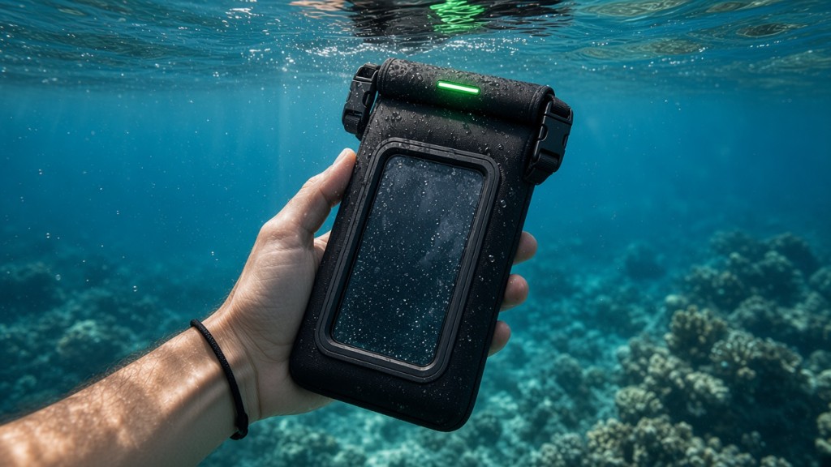
blueprints/pitch/in-use-underwater.jpg
