bei22002-cpu/pocketvault-d14/blueprints/pitch/kit-flat.jpg

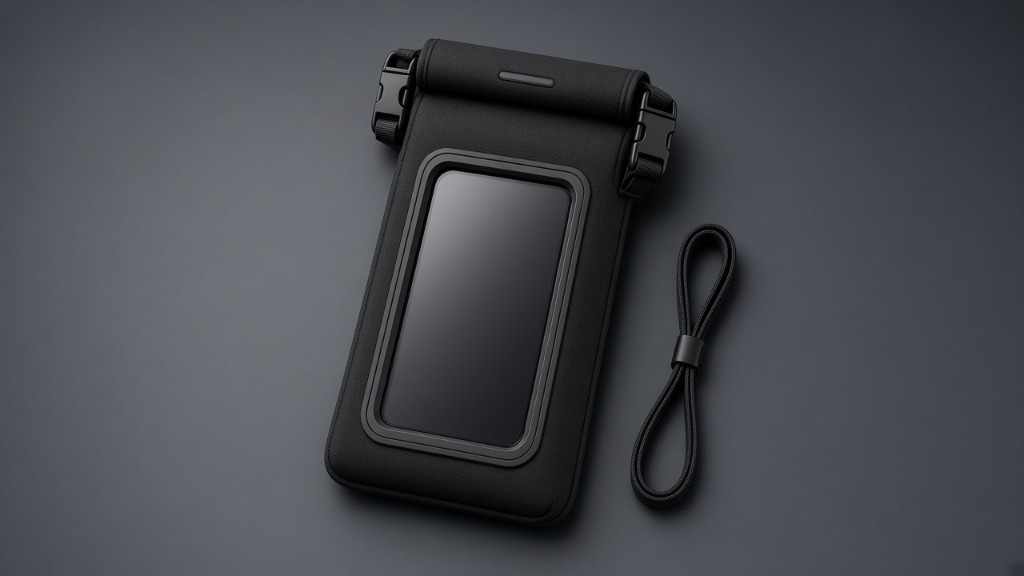
blueprints/pitch/kit-flat.jpg
