bei22002-cpu/pocketvault-d14/blueprints/pitch/open-loading.png

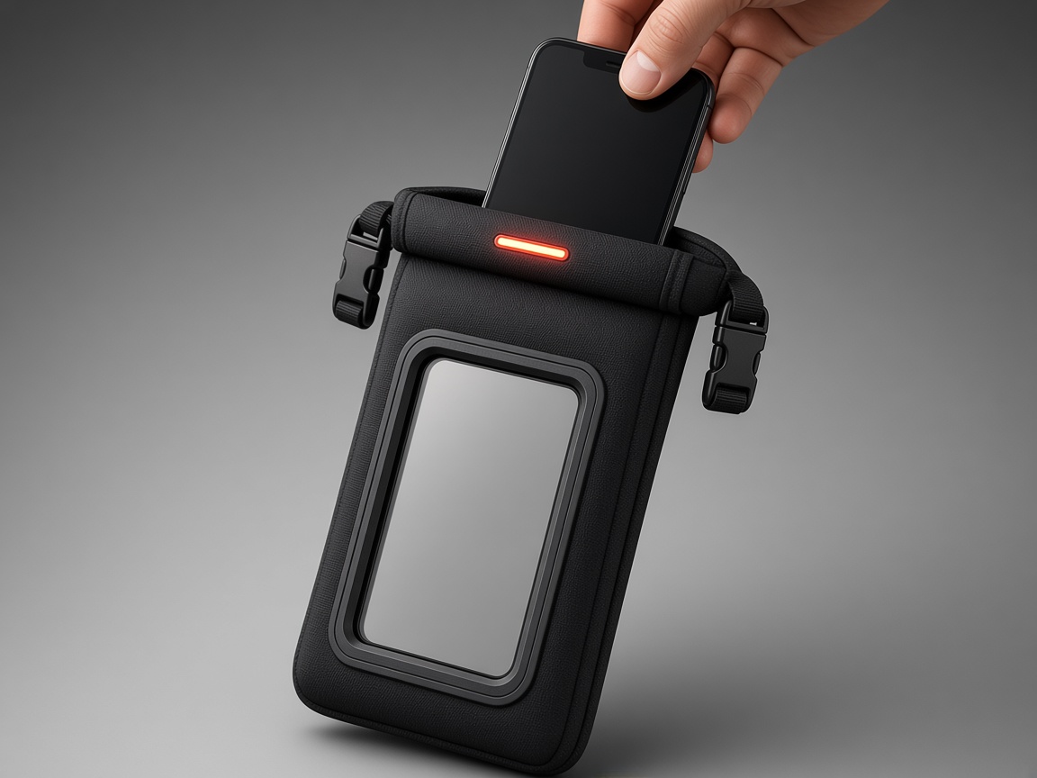
blueprints/pitch/open-loading.png
