bei22002-cpu/pocketvault-d14/blueprints/products/product-A1-lightline-mg.png

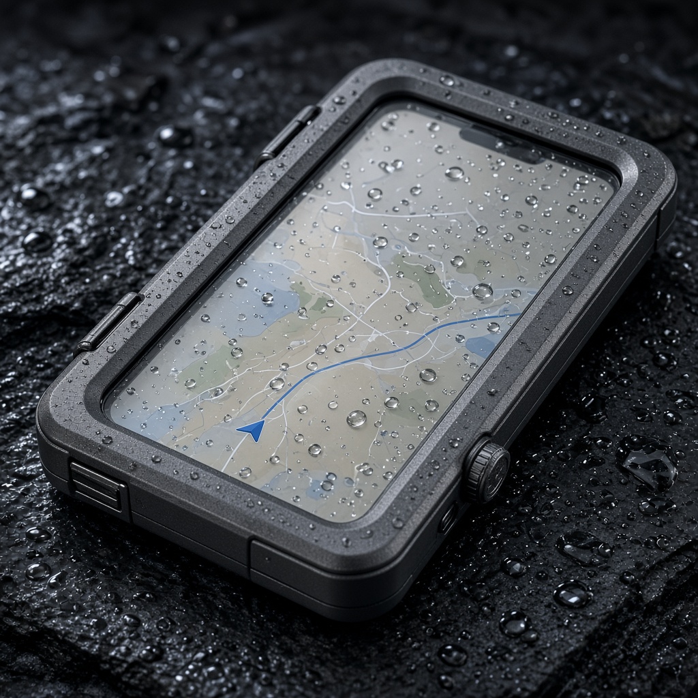
blueprints/products/product-A1-lightline-mg.png
