bei22002-cpu/pocketvault-d14/blueprints/products/product-A2-carbonshell.png

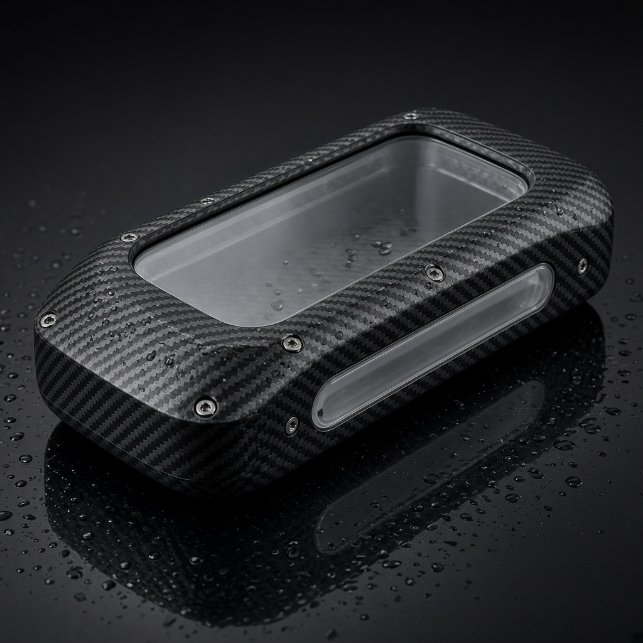
blueprints/products/product-A2-carbonshell.png
