bei22002-cpu/pocketvault-d14/blueprints/products/product-A3-skeleton.png

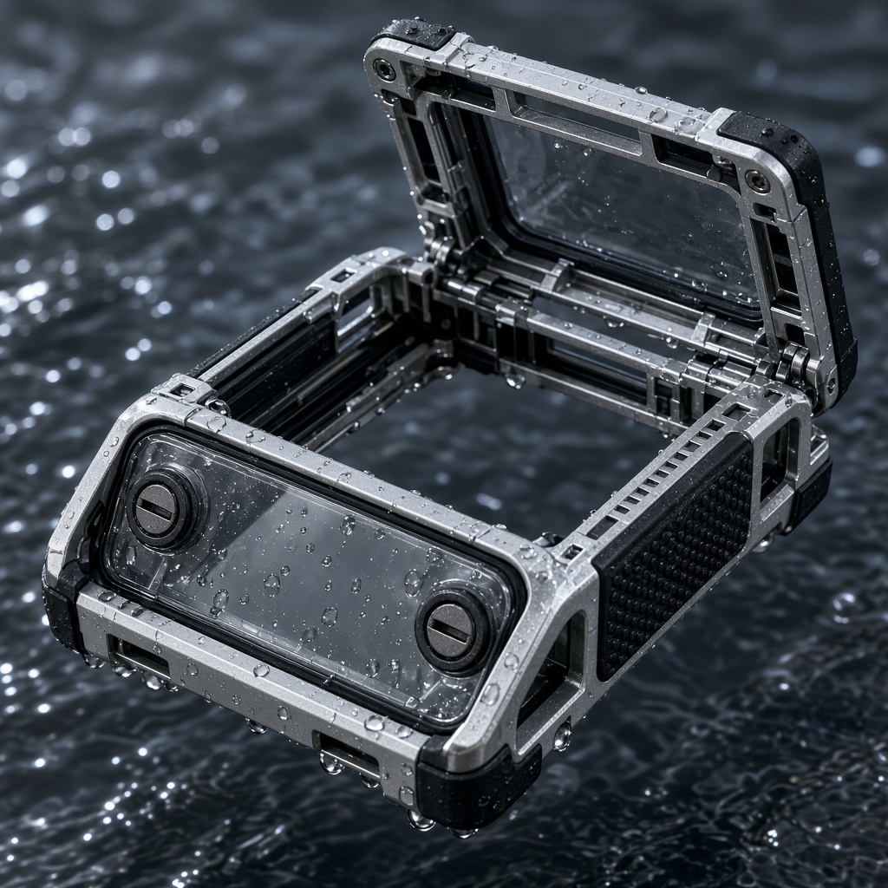
blueprints/products/product-A3-skeleton.png
