bei22002-cpu/pocketvault-d14/blueprints/products/product-A4-titan-20.png

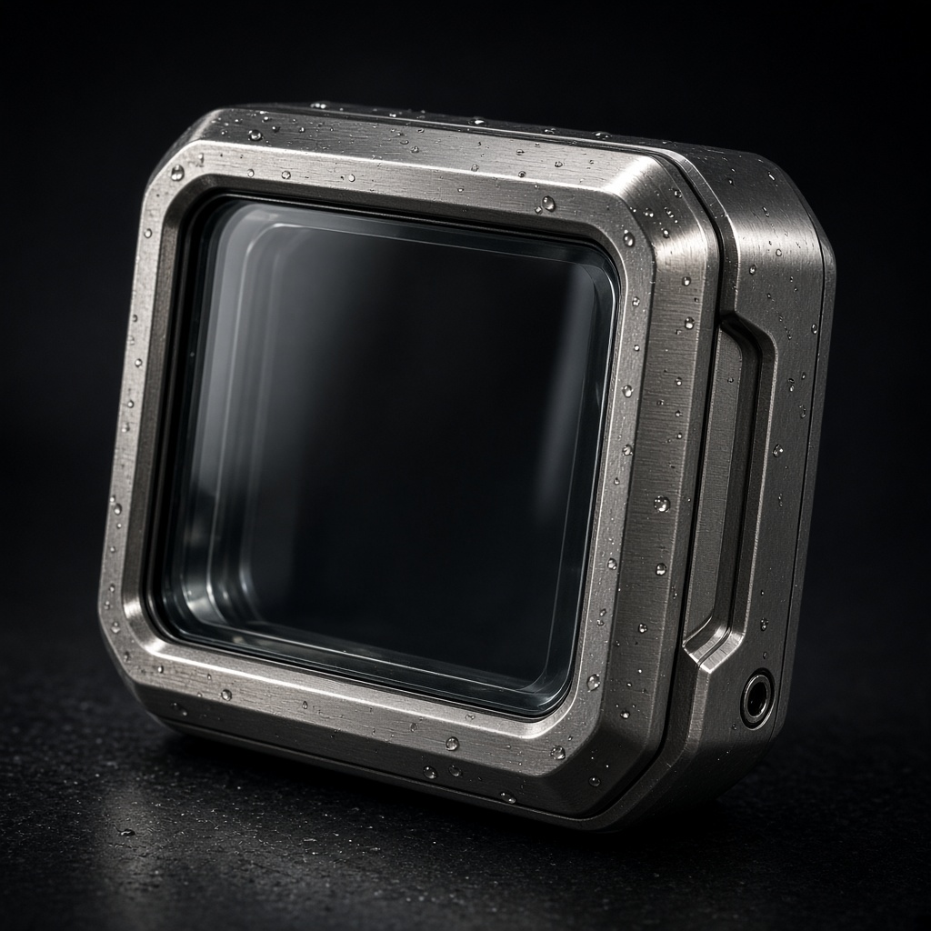
blueprints/products/product-A4-titan-20.png
