bei22002-cpu/pocketvault-d14/blueprints/products/product-B5-hall-glove.png

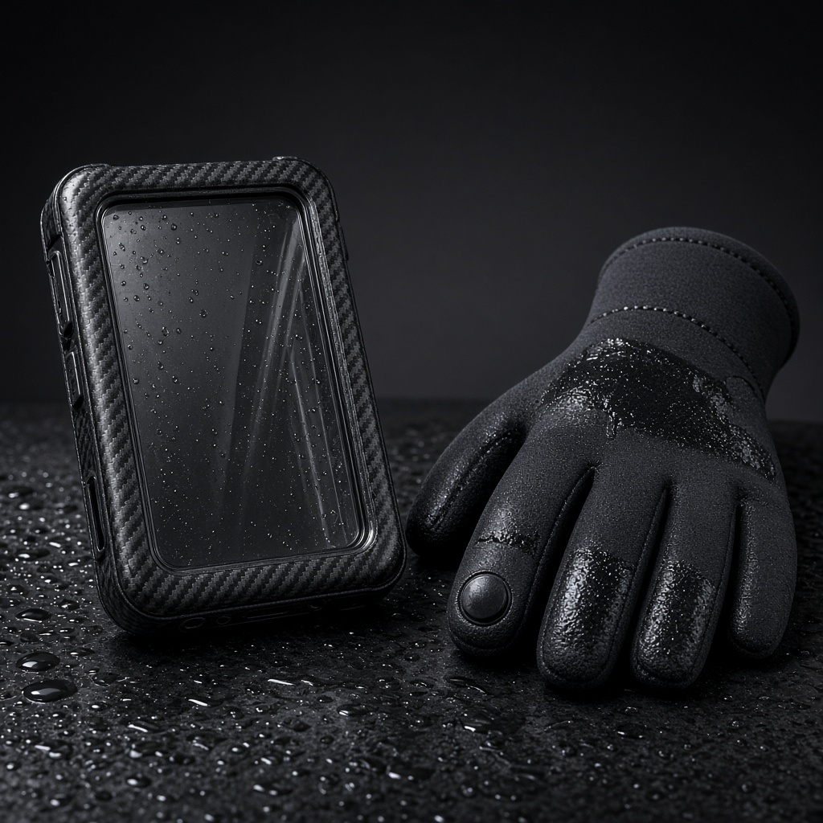
blueprints/products/product-B5-hall-glove.png
