bei22002-cpu/pocketvault-d14/blueprints/products/product-B6-stylus-emr.png

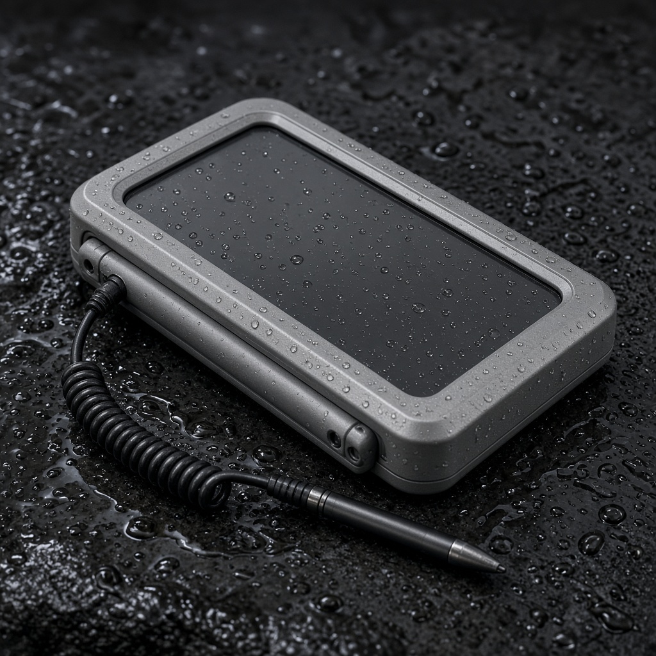
blueprints/products/product-B6-stylus-emr.png
