bei22002-cpu/pocketvault-d14/blueprints/products/product-B7-lamb-wave.png

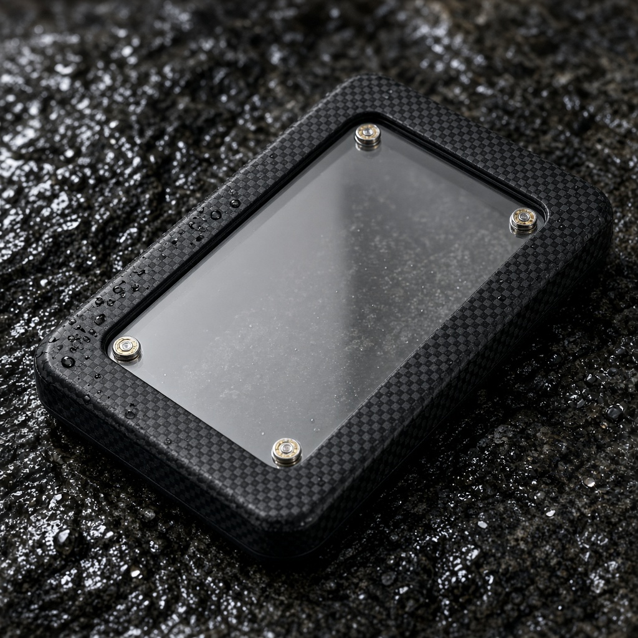
blueprints/products/product-B7-lamb-wave.png
