bei22002-cpu/pocketvault-d14/blueprints/products/product-B8-resistive-hard.png

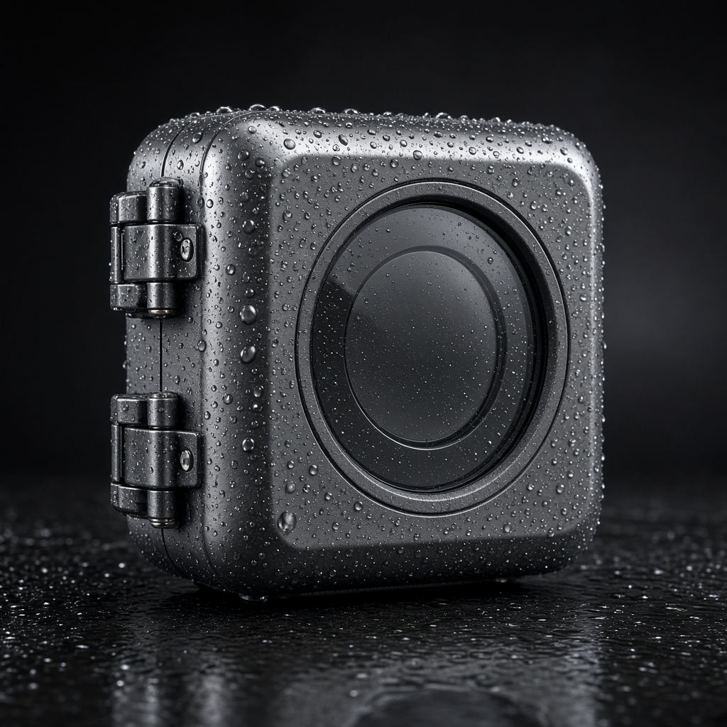
blueprints/products/product-B8-resistive-hard.png
