bei22002-cpu/pocketvault-d14/blueprints/products/product-B9-gap-cap.png

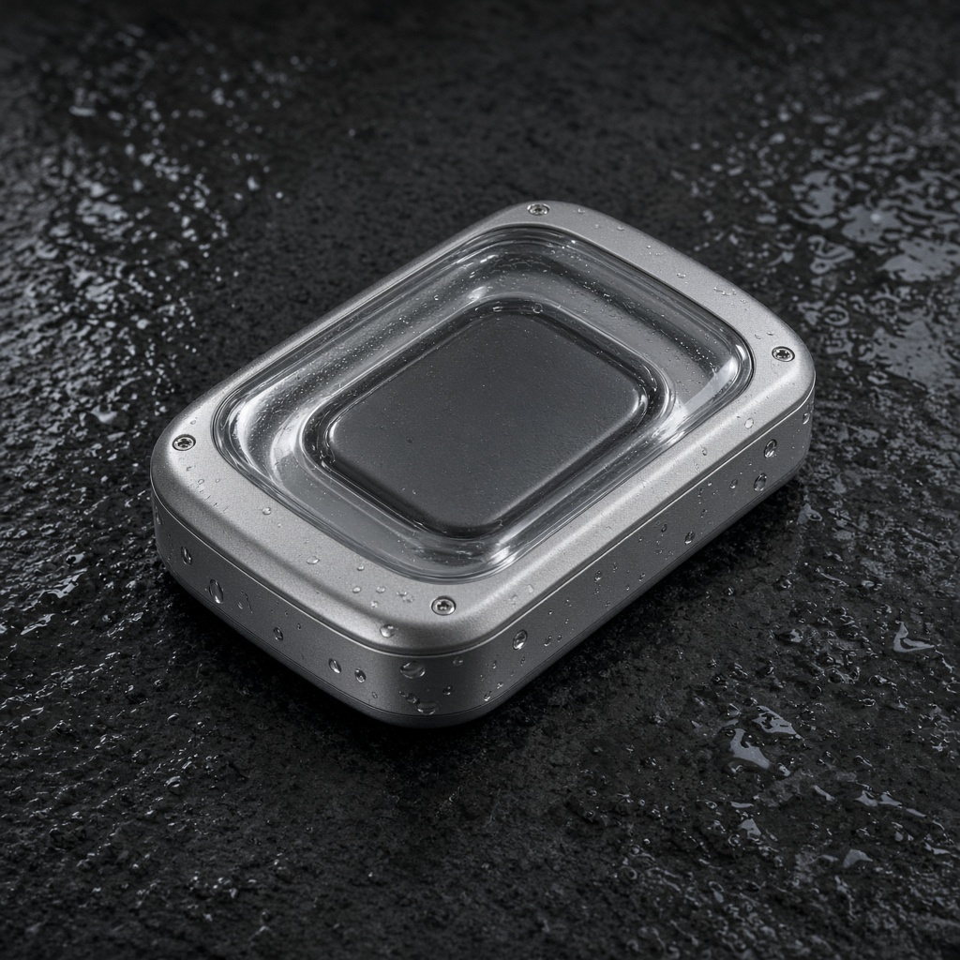
blueprints/products/product-B9-gap-cap.png
