bei22002-cpu/pocketvault-d14/blueprints/products/product-C10-crownpad.png

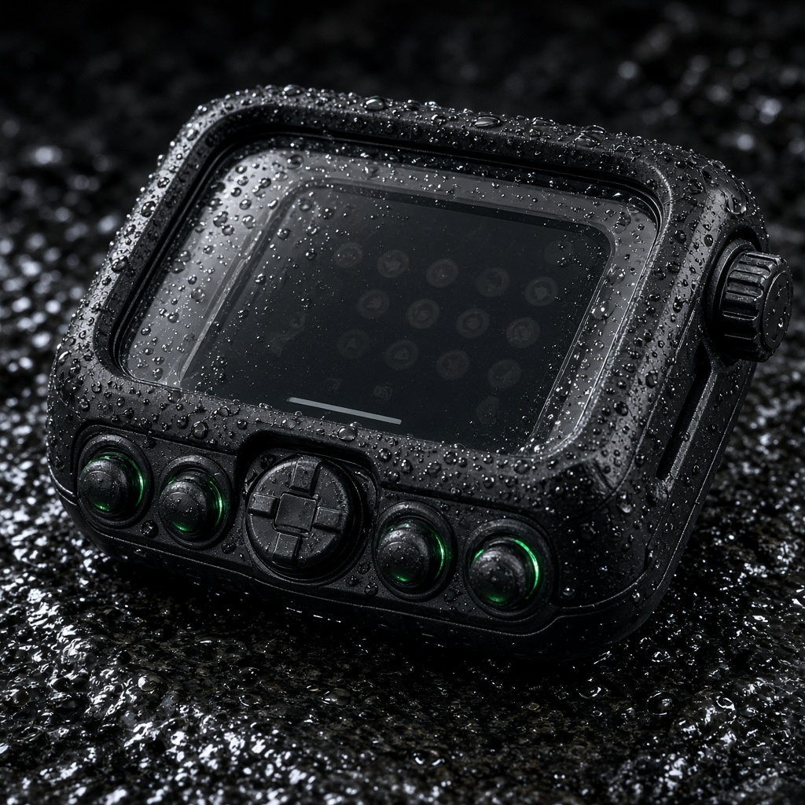
blueprints/products/product-C10-crownpad.png
