bei22002-cpu/pocketvault-d14/blueprints/products/product-C11-tether-puck.png

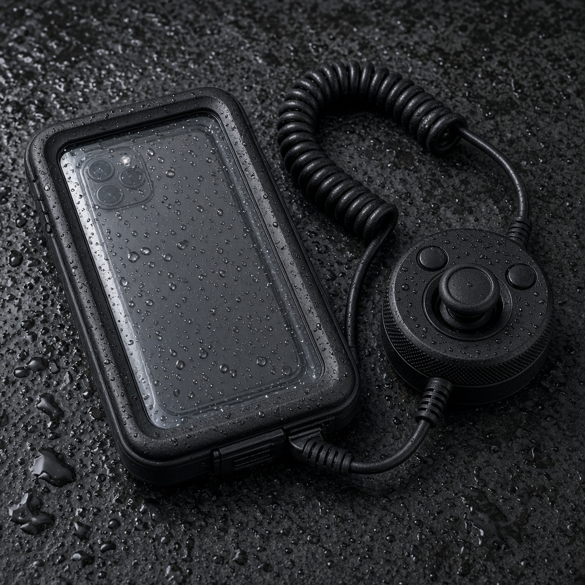
blueprints/products/product-C11-tether-puck.png
