bei22002-cpu/pocketvault-d14/blueprints/products/product-C12-tilt-cursor.png

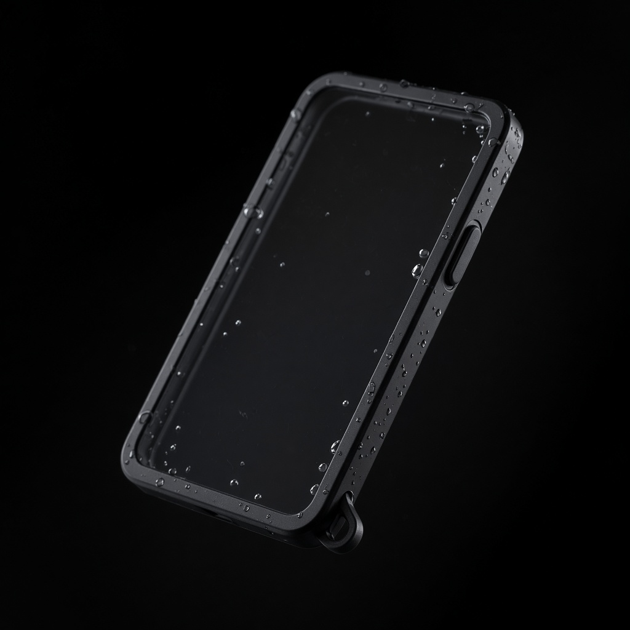
blueprints/products/product-C12-tilt-cursor.png
