bei22002-cpu/pocketvault-d14/blueprints/products/product-C13-voice-ptt.png

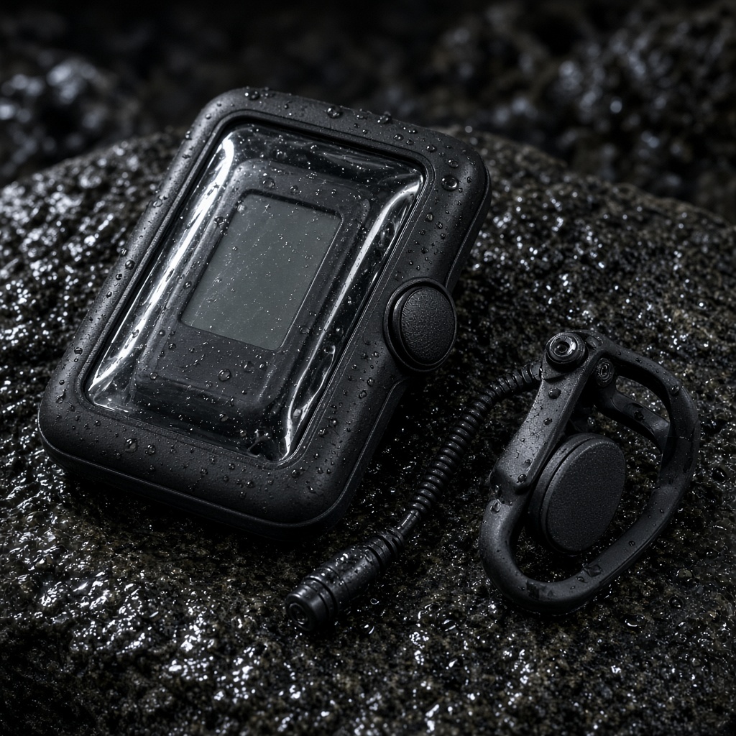
blueprints/products/product-C13-voice-ptt.png
