bei22002-cpu/pocketvault-d14/blueprints/products/product-D14-rolltop.png

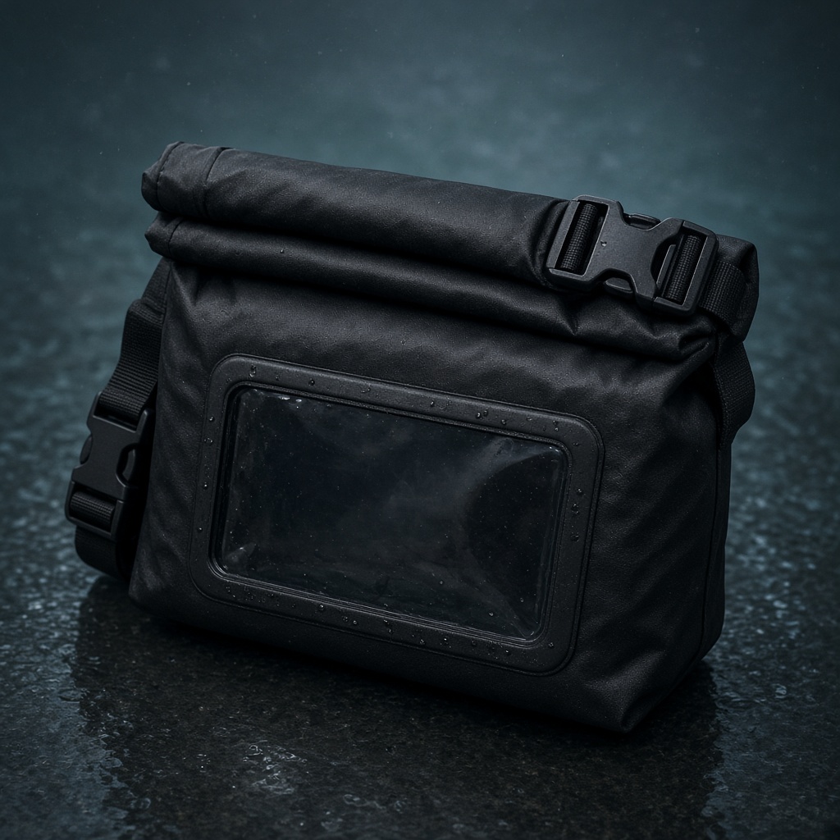
blueprints/products/product-D14-rolltop.png
