bei22002-cpu/pocketvault-d14/blueprints/products/product-D15-oilfill-100.png

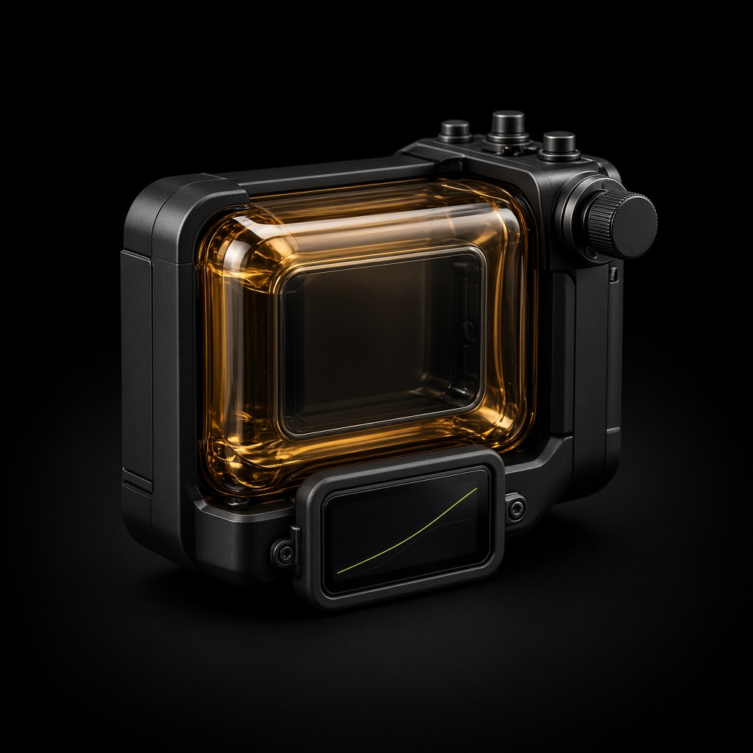
blueprints/products/product-D15-oilfill-100.png
