bei22002-cpu/pocketvault-d14/blueprints/products/product-D16-floatline.png

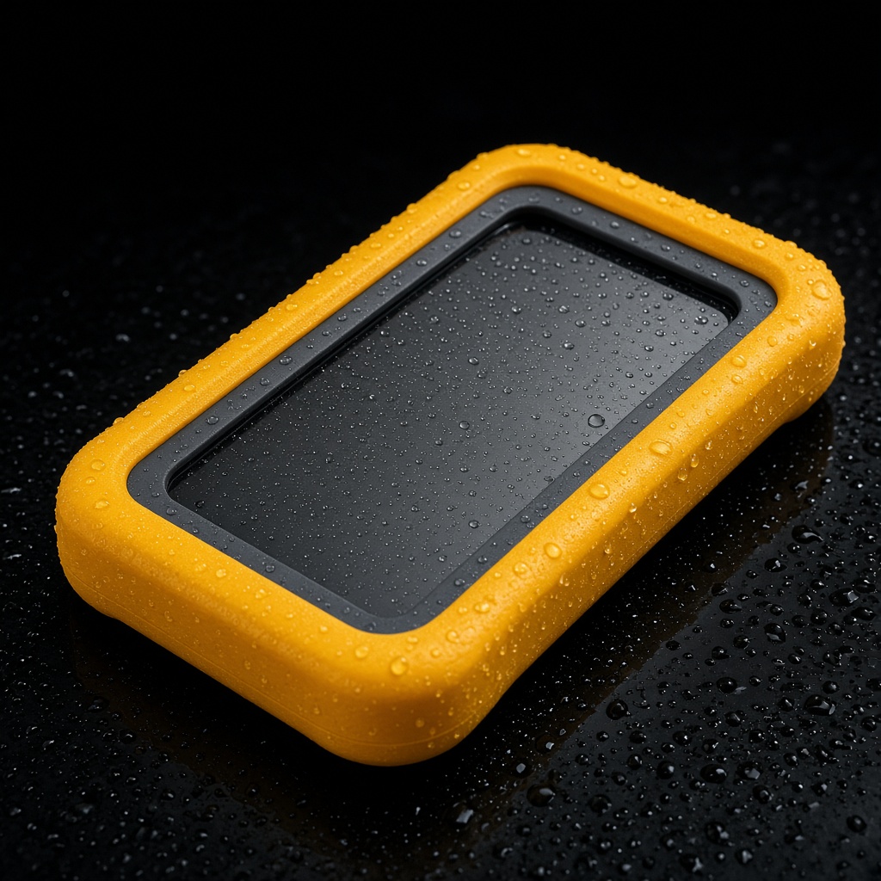
blueprints/products/product-D16-floatline.png
