bei22002-cpu/pocketvault-d14/blueprints/products/product-D17-chestboard.png

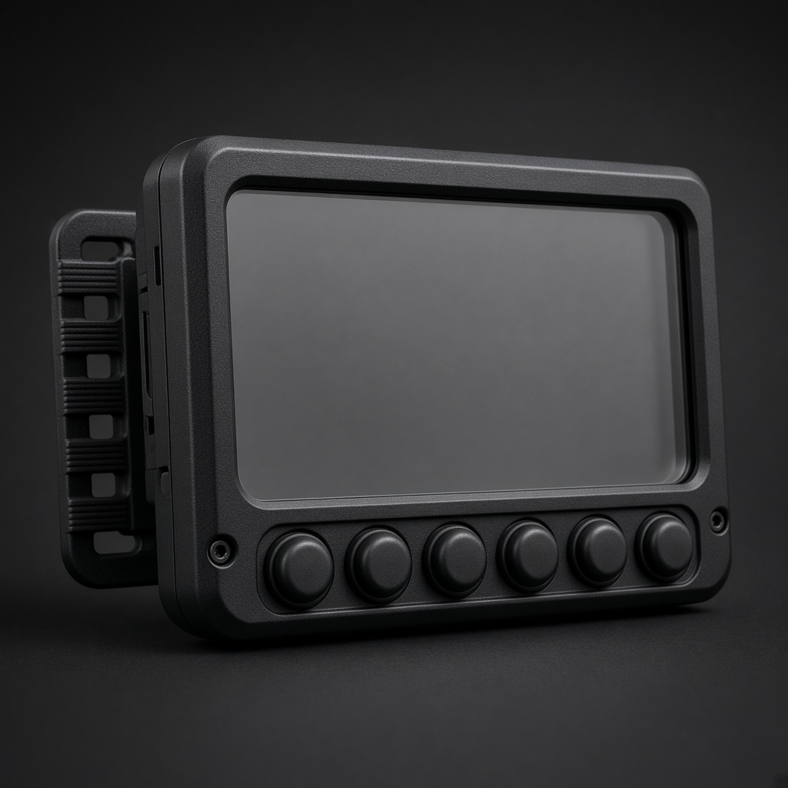
blueprints/products/product-D17-chestboard.png
