bei22002-cpu/pocketvault-d14/blueprints/products/product-D18-gauntlet.png

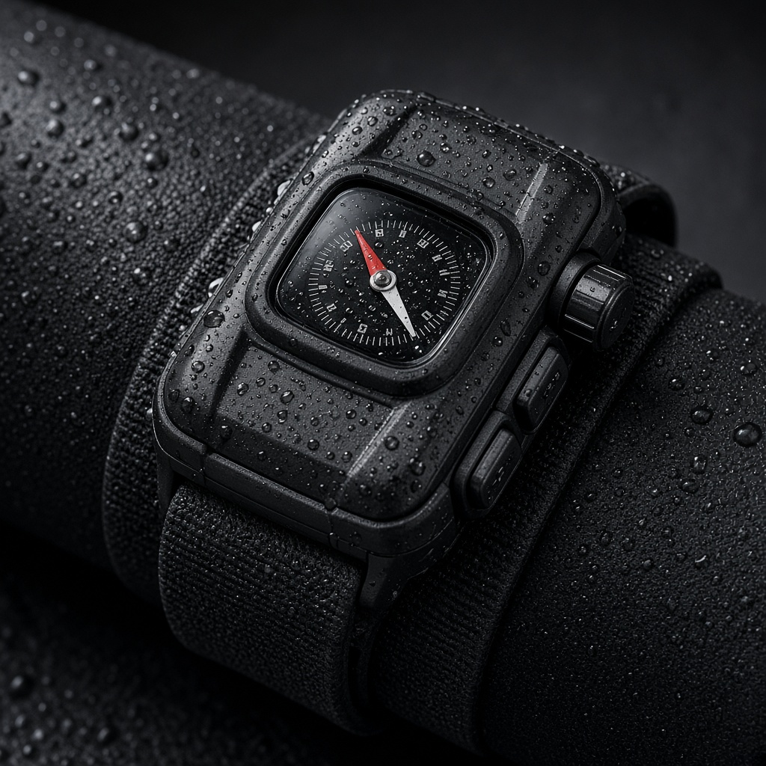
blueprints/products/product-D18-gauntlet.png
