bei22002-cpu/pocketvault-d14/blueprints/rolltop/reference/D14-rolltop-revB-drawing.png

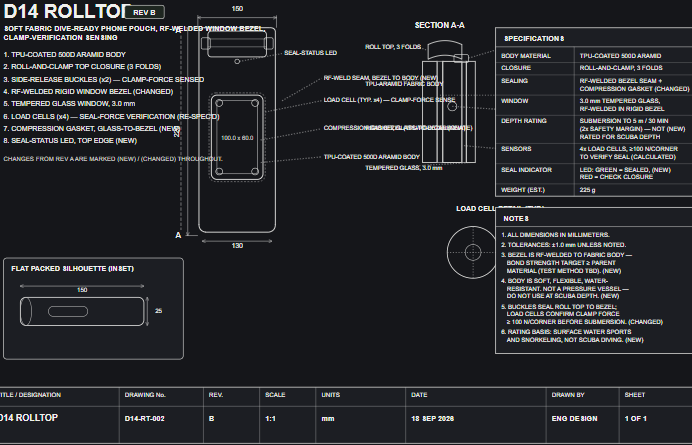
blueprints/rolltop/reference/D14-rolltop-revB-drawing.png
