bei22002-cpu/pocketvault-d14/blueprints/rolltop/reference/original-sketch.png

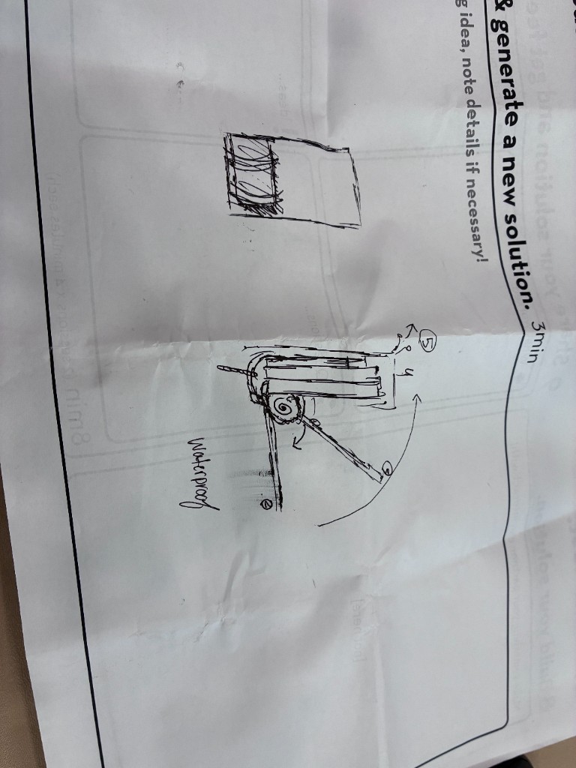
blueprints/rolltop/reference/original-sketch.png
