bei22002-cpu/pocketvault-d14/blueprints/rolltop/renders/_view-notes.png

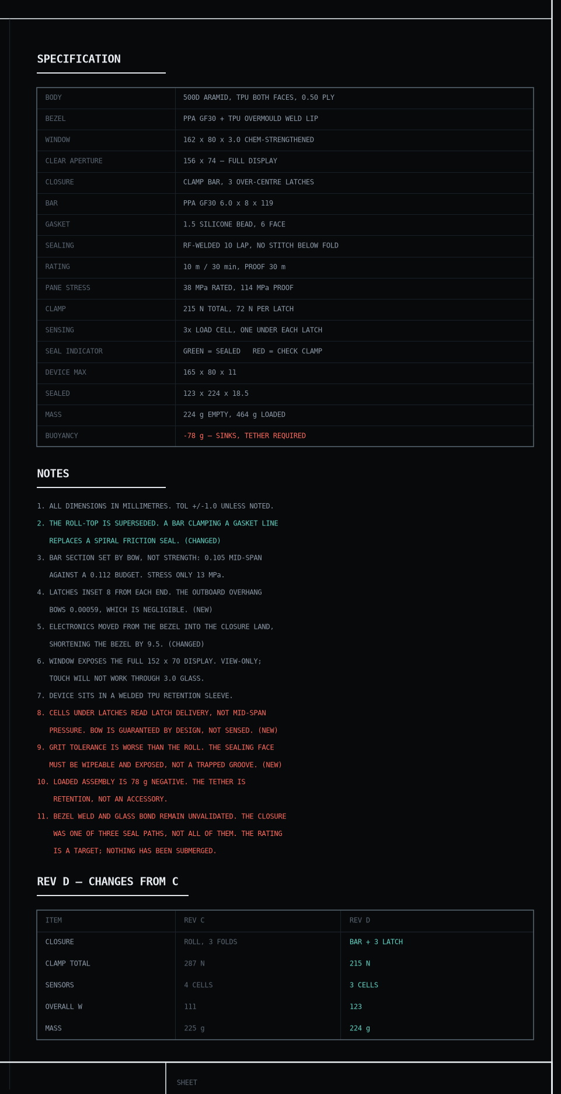
blueprints/rolltop/renders/_view-notes.png
