bei22002-cpu/pocketvault-d14/blueprints/rolltop/renders/D14-RT-003-revC.png

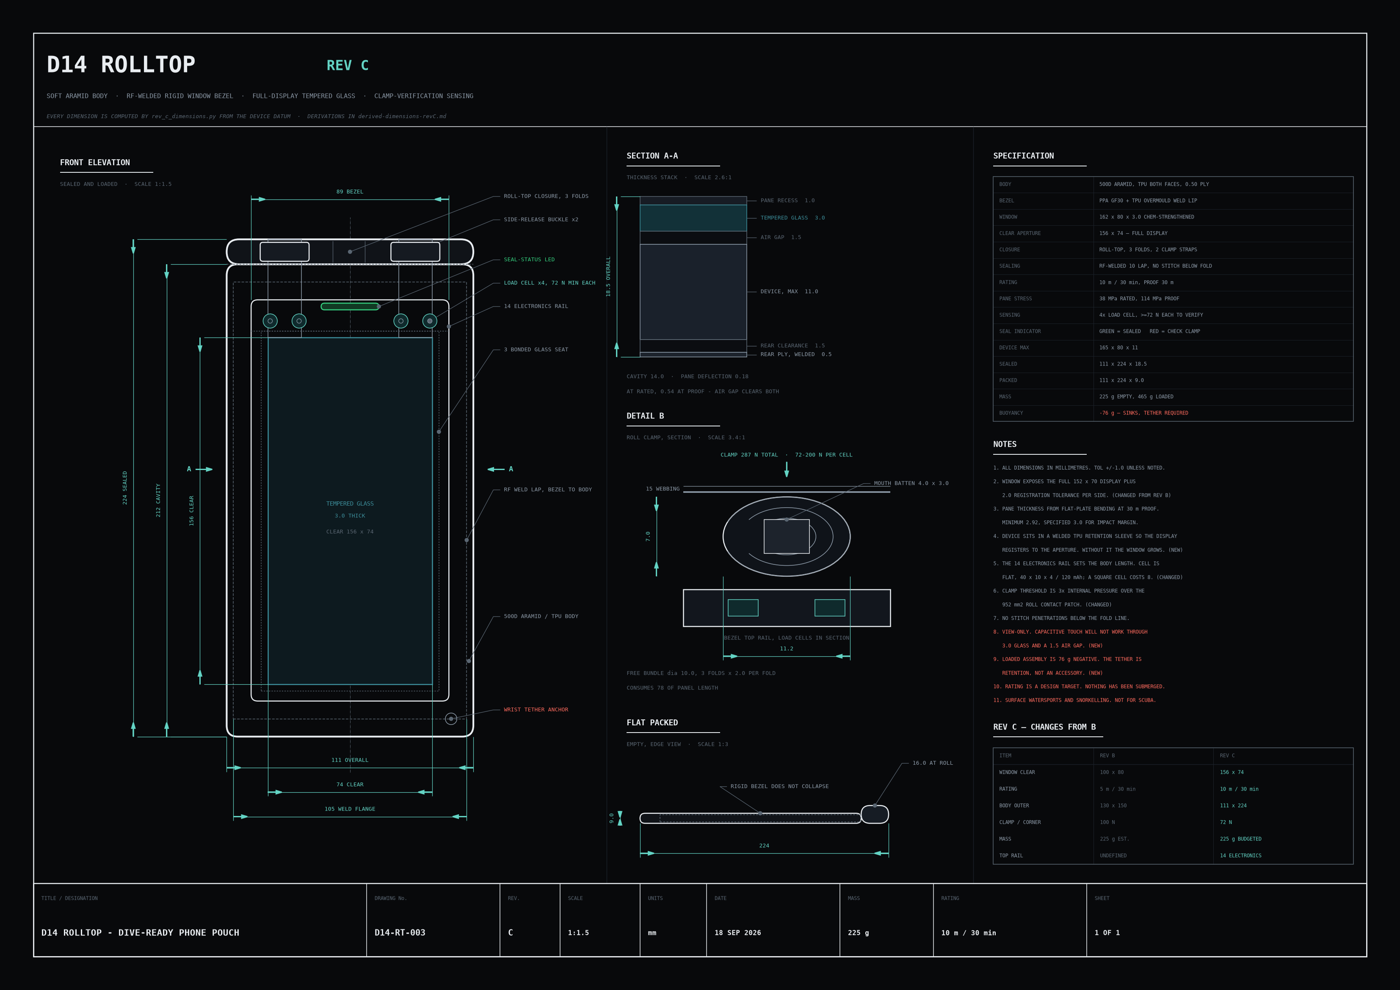
blueprints/rolltop/renders/D14-RT-003-revC.png
