bei22002-cpu/pocketvault-d14/blueprints/rolltop/renders/deployment-sequence.png

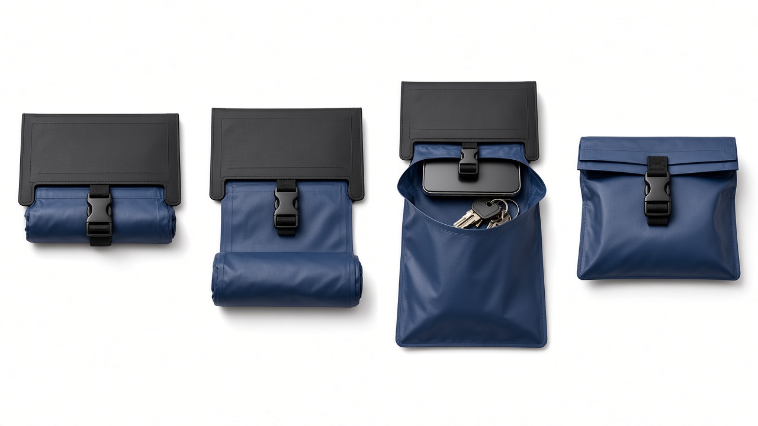
blueprints/rolltop/renders/deployment-sequence.png
