bei22002-cpu/pocketvault-d14/blueprints/rolltop/renders/hero-render.png

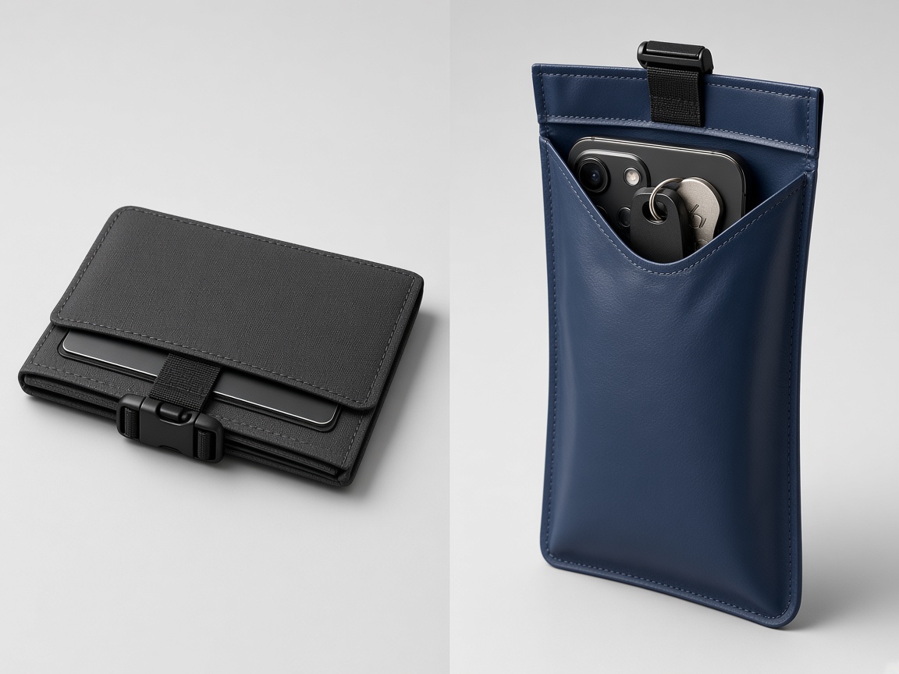
blueprints/rolltop/renders/hero-render.png
