bei22002-cpu/pocketvault-d14/blueprints/rolltop/renders/northstar_wallet_deployed_iso.png

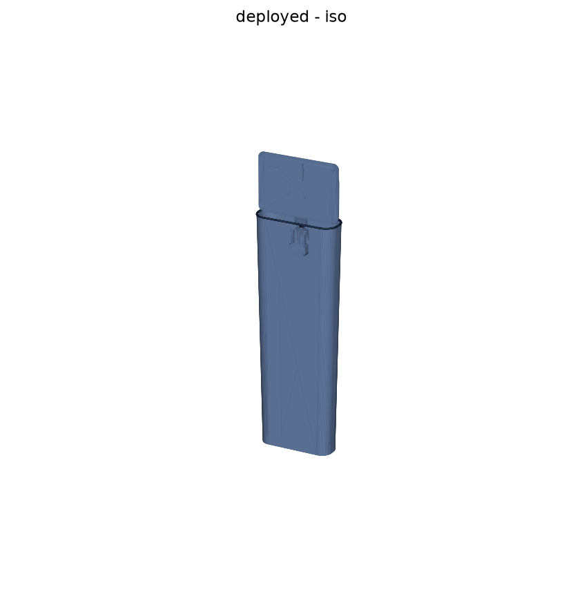
blueprints/rolltop/renders/northstar_wallet_deployed_iso.png
