bei22002-cpu/pocketvault-d14/blueprints/rolltop/renders/northstar_wallet_stowed_side.png

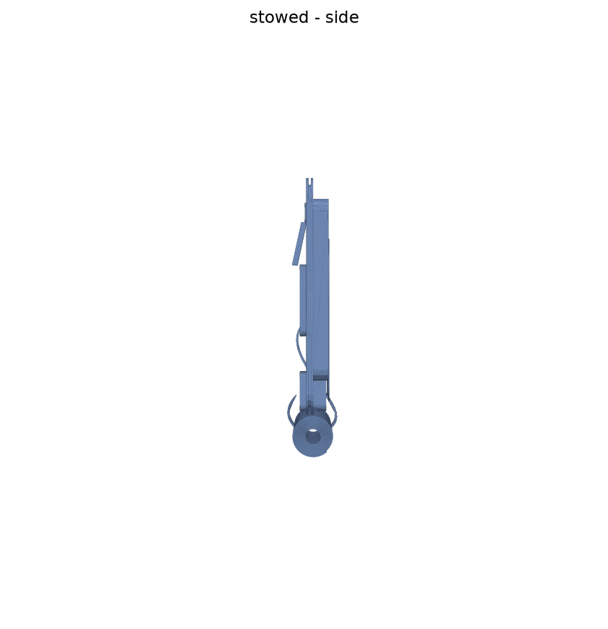
blueprints/rolltop/renders/northstar_wallet_stowed_side.png
