bei22002-cpu/pocketvault-d14/blueprints/rolltop/renders/revD-detail-clamp-macro.png

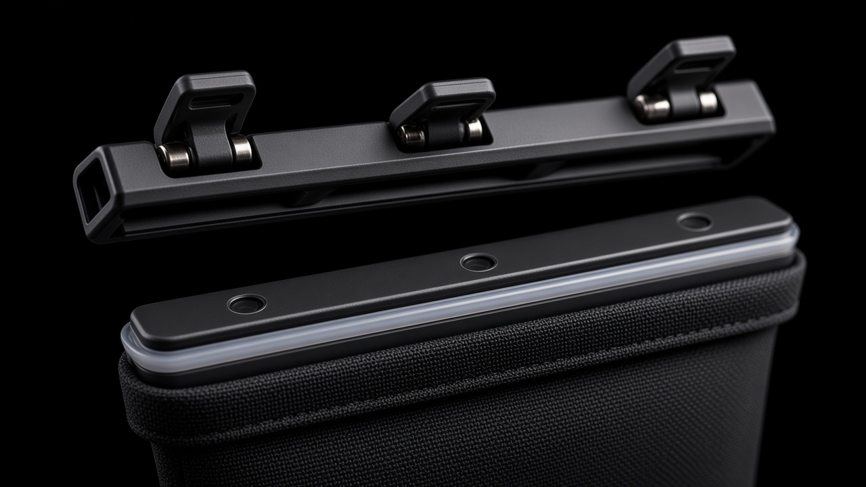
blueprints/rolltop/renders/revD-detail-clamp-macro.png
