bei22002-cpu/pocketvault-d14/blueprints/rolltop/renders/revD-lifestyle-underwater.png

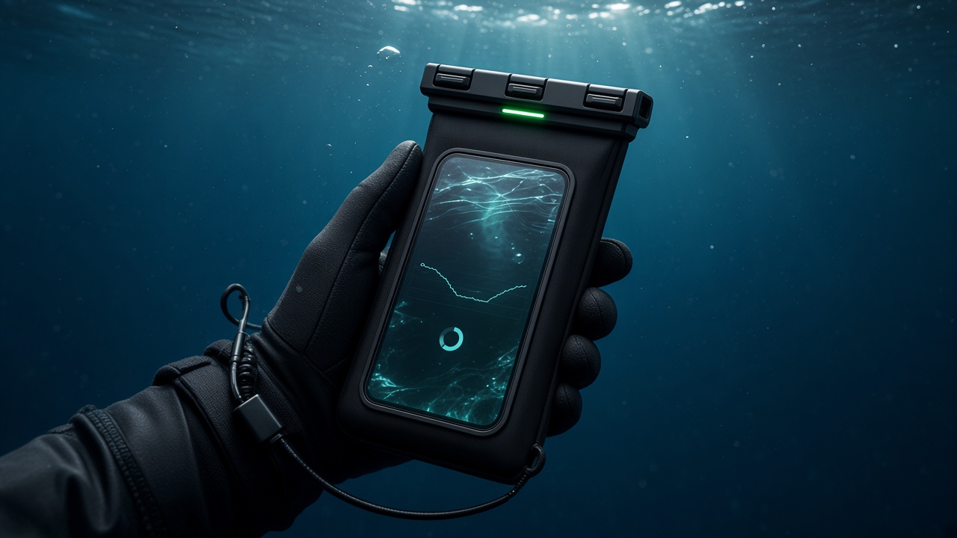
blueprints/rolltop/renders/revD-lifestyle-underwater.png
