bei22002-cpu/pocketvault-d14/blueprints/rolltop/renders/revD-open-loading.png

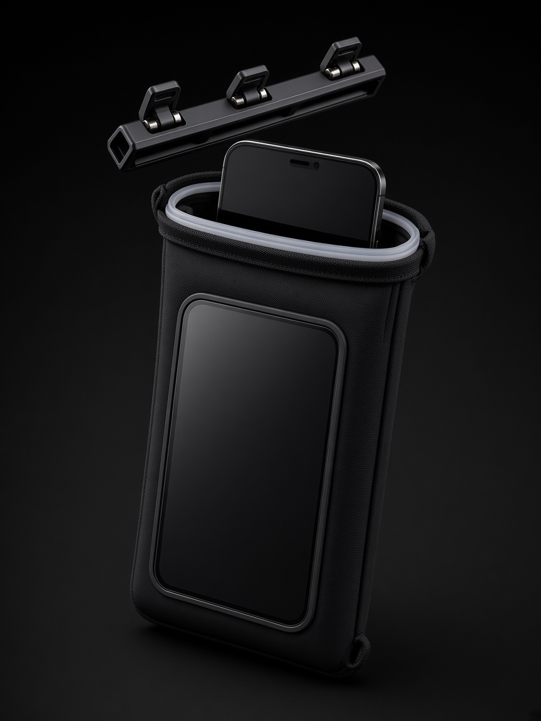
blueprints/rolltop/renders/revD-open-loading.png
