bei22002-cpu/pocketvault-d14/blueprints/models/A3/window_cartridge.step

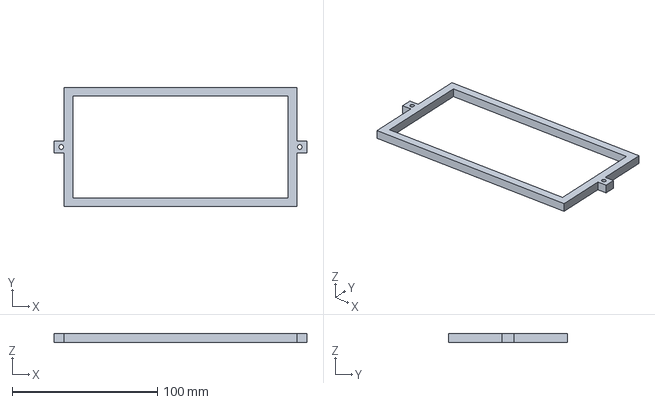
[picture p124: CAD file, 2026-09-18]
blueprints/models/A3/window_cartridge.step
174.0 x 82.0 x 6.00 mm
