bei22002-cpu/pocketvault-d14/blueprints/models/A4/window_blank.step

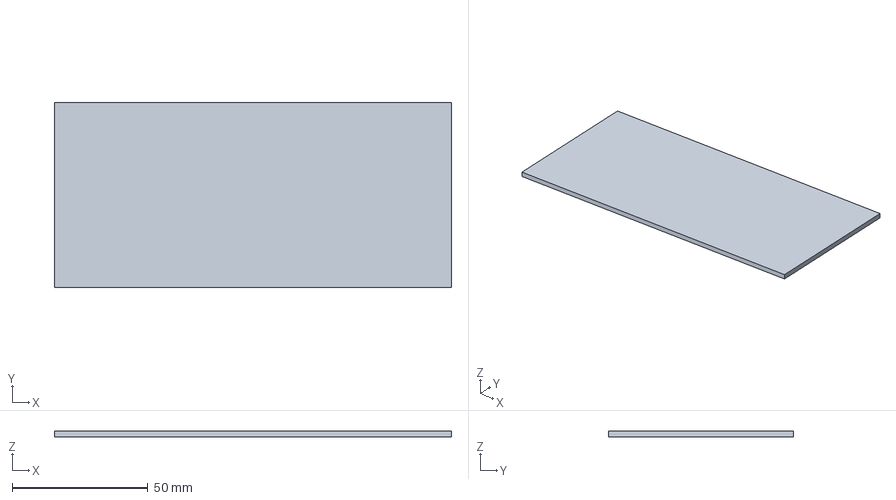
[picture p125: CAD file, 2026-09-18]
blueprints/models/A4/window_blank.step
146.0 x 68.0 x 2.20 mm
