bei22002-cpu/pocketvault-d14/blueprints/models/B6/shell_back.step

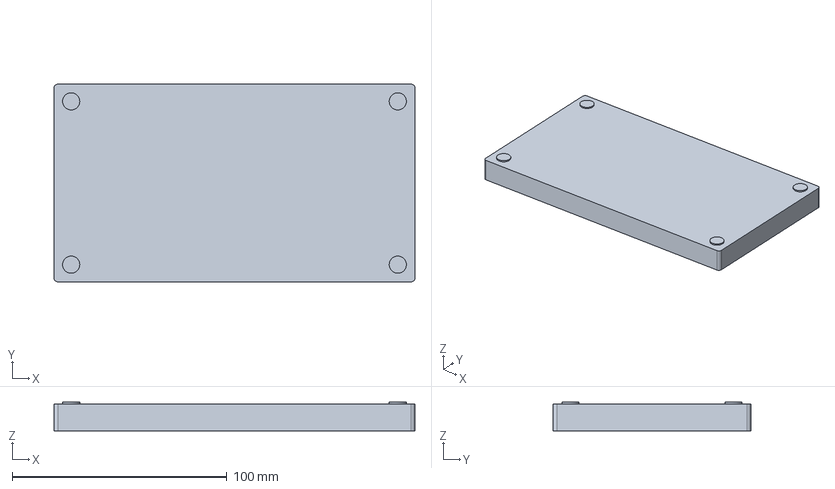
[picture p126: CAD file, 2026-09-18]
blueprints/models/B6/shell_back.step
168.0 x 92.0 x 13.3 mm
