bei22002-cpu/pocketvault-d14/blueprints/models/C10/shell_back.step

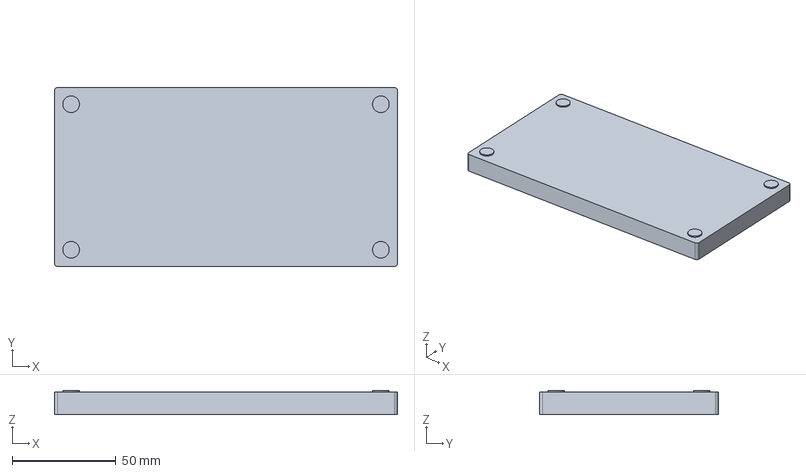
[picture p127: CAD file, 2026-09-18]
blueprints/models/C10/shell_back.step
165.0 x 86.0 x 11.6 mm
