bei22002-cpu/pocketvault-d14/blueprints/models/C11/tether_puck.step

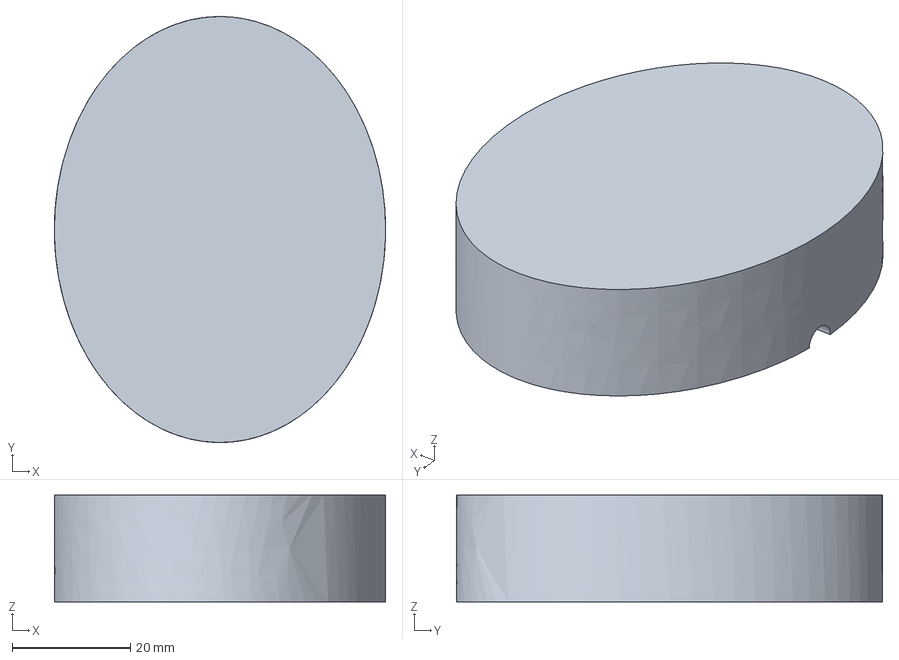
[picture p128: CAD file, 2026-09-18]
blueprints/models/C11/tether_puck.step
56.0 x 72.0 x 18.0 mm
