bei22002-cpu/pocketvault-d14/blueprints/models/C12/shell_front.step

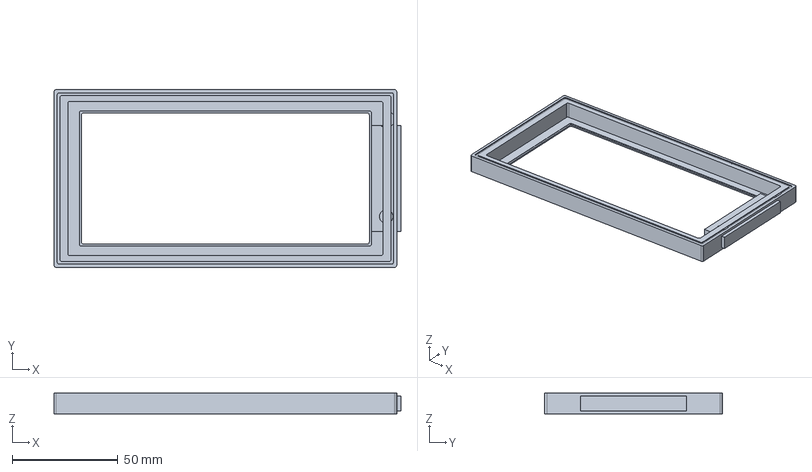
[picture p129: CAD file, 2026-09-18]
blueprints/models/C12/shell_front.step
164.0 x 84.0 x 9.90 mm
