bei22002-cpu/pocketvault-d14/blueprints/models/C13/shell_front.step

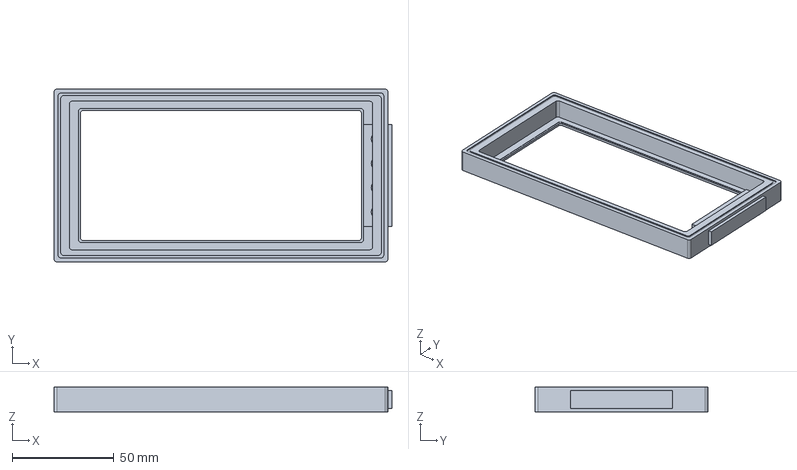
[picture p130: CAD file, 2026-09-18]
blueprints/models/C13/shell_front.step
166.0 x 85.0 x 12.1 mm
