bei22002-cpu/pocketvault-d14/blueprints/models/D15/oil_shell.step

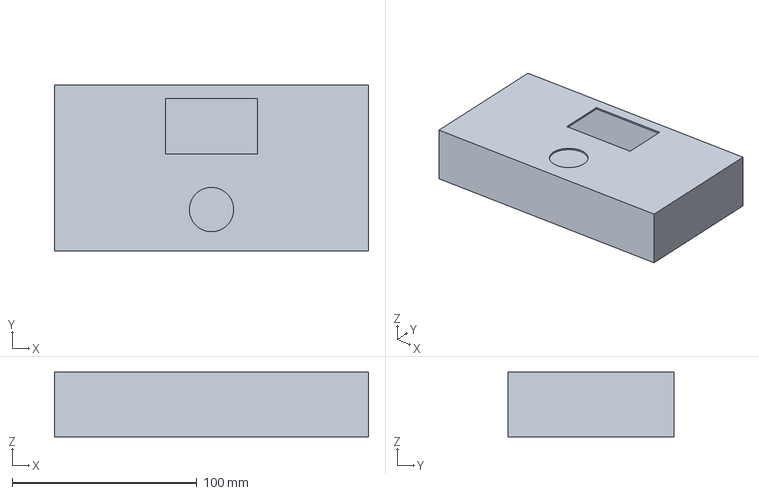
[picture p131: CAD file, 2026-09-18]
blueprints/models/D15/oil_shell.step
170.0 x 90.0 x 35.0 mm
