bei22002-cpu/pocketvault-d14/blueprints/models/D17/window_blank.step

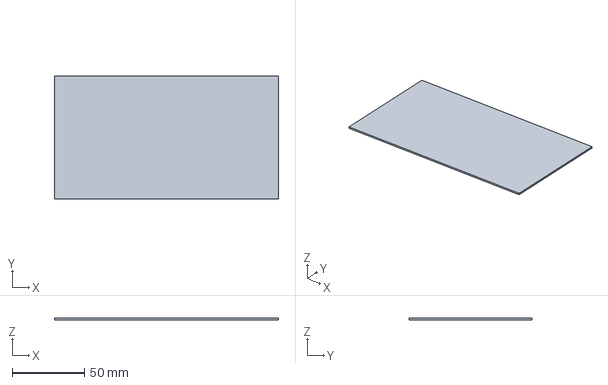
[picture p132: CAD file, 2026-09-18]
blueprints/models/D17/window_blank.step
155.0 x 85.0 x 1.20 mm
