bei22002-cpu/pocketvault-d14/blueprints/models/D18/shell_back.step

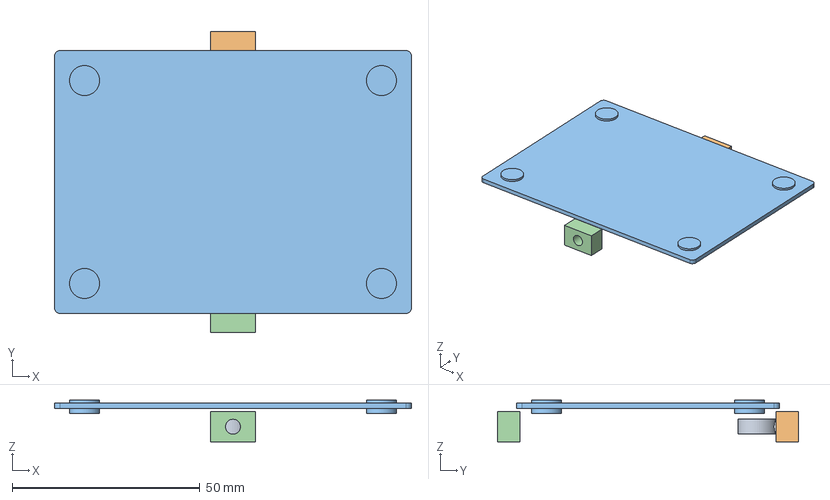
[picture p133: CAD file, 2026-09-18]
blueprints/models/D18/shell_back.step
95.0 x 80.0 x 11.1 mm
