bei22002-cpu/pocketvault-d14/blueprints/models/A3/rib_cage.step

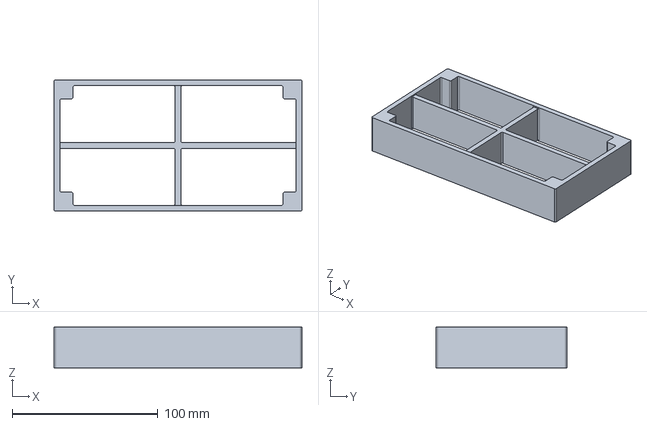
[picture p134: CAD file, 2026-09-18]
blueprints/models/A3/rib_cage.step
170.0 x 90.0 x 28.0 mm
