bei22002-cpu/pocketvault-d14/blueprints/models/A4/shell_front.step

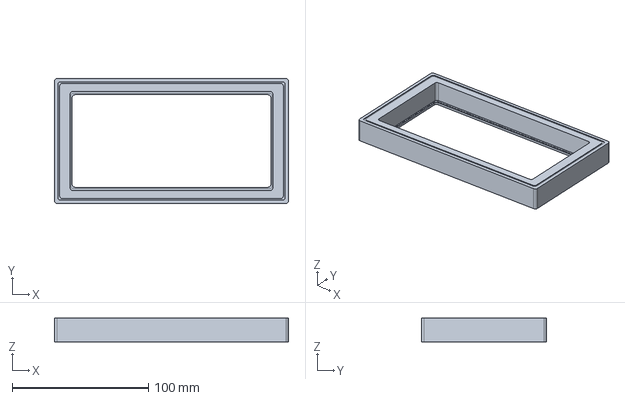
[picture p135: CAD file, 2026-09-18]
blueprints/models/A4/shell_front.step
172.0 x 92.0 x 17.6 mm
