bei22002-cpu/pocketvault-d14/blueprints/models/C10/window_blank.step

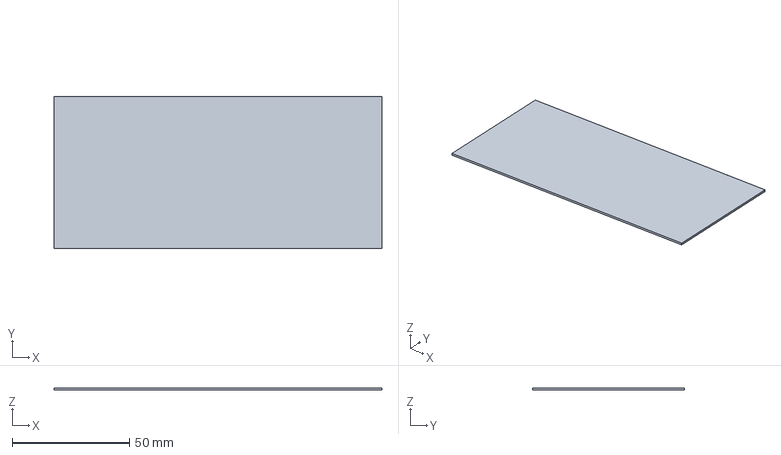
[picture p136: CAD file, 2026-09-18]
blueprints/models/C10/window_blank.step
140.0 x 65.0 x 1.00 mm
