bei22002-cpu/pocketvault-d14/blueprints/models/C11/window_blank.step

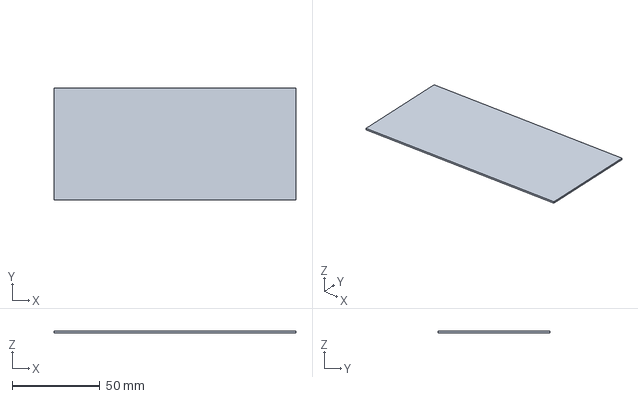
[picture p137: CAD file, 2026-09-18]
blueprints/models/C11/window_blank.step
138.0 x 64.0 x 1.00 mm
