bei22002-cpu/pocketvault-d14/blueprints/models/C12/shell_back.step

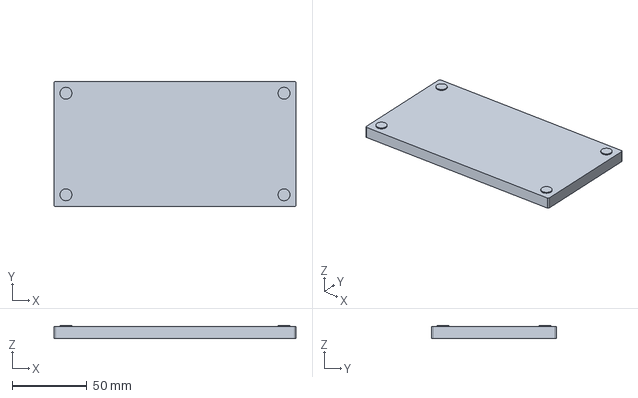
[picture p138: CAD file, 2026-09-18]
blueprints/models/C12/shell_back.step
162.0 x 84.0 x 8.85 mm
