bei22002-cpu/pocketvault-d14/blueprints/models/D14/rigid_bezel.step

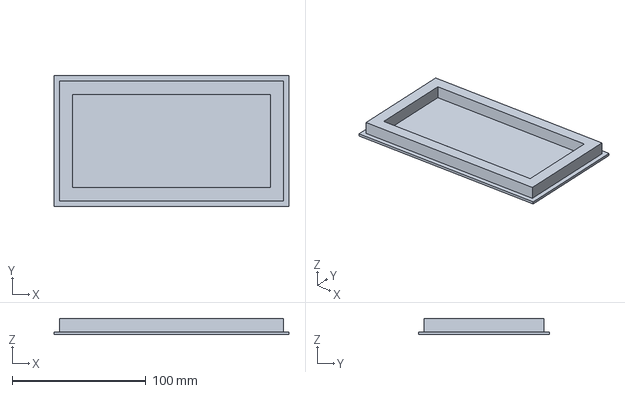
[picture p139: CAD file, 2026-09-18]
blueprints/models/D14/rigid_bezel.step
176.0 x 98.0 x 12.0 mm
