bei22002-cpu/pocketvault-d14/blueprints/models/D16/foam_collar.step

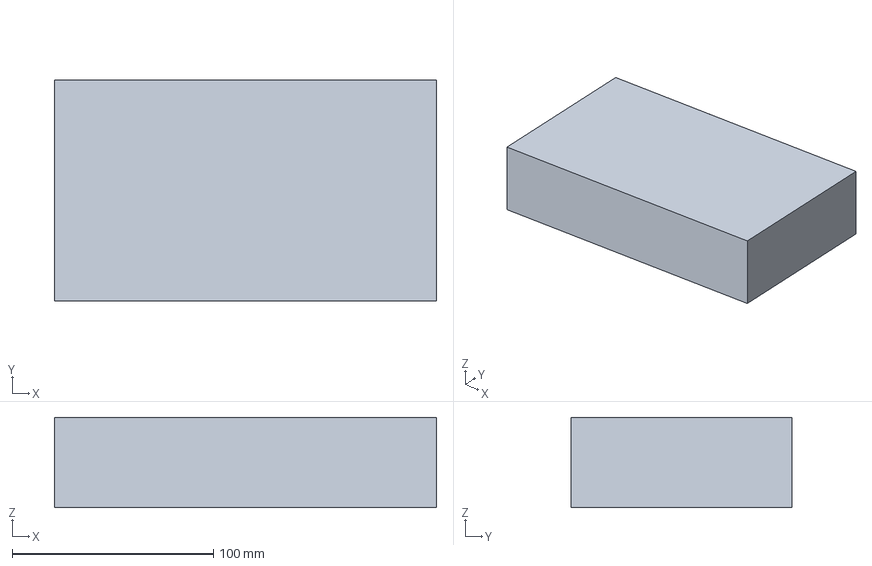
[picture p140: CAD file, 2026-09-18]
blueprints/models/D16/foam_collar.step
190.0 x 110.0 x 45.0 mm
