bei22002-cpu/pocketvault-d14/blueprints/models/D17/shell_back.step

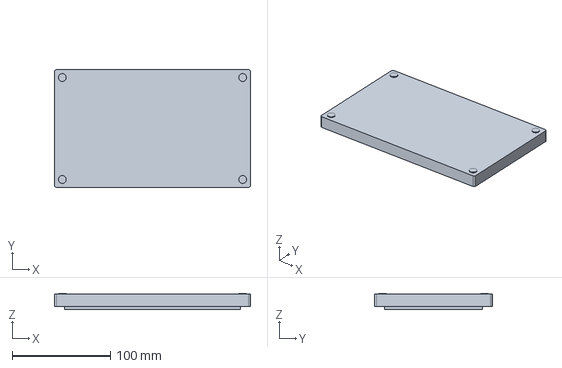
[picture p141: CAD file, 2026-09-18]
blueprints/models/D17/shell_back.step
200.0 x 120.0 x 16.4 mm
