bei22002-cpu/pocketvault-d14/blueprints/models/D18/window_blank.step

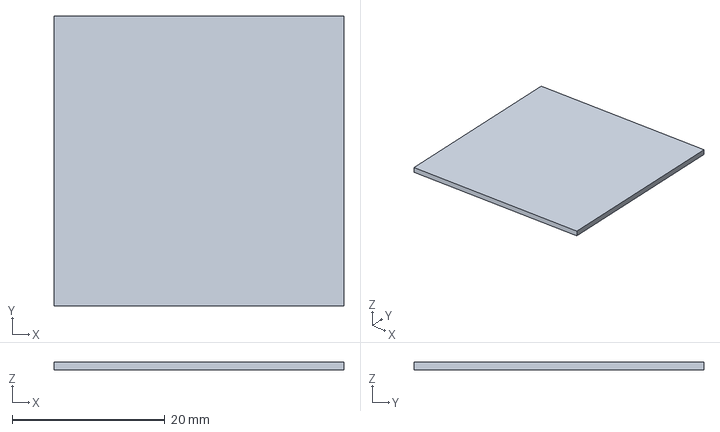
[picture p142: CAD file, 2026-09-18]
blueprints/models/D18/window_blank.step
38.0 x 38.0 x 1.00 mm
