bei22002-cpu/pocketvault-d14/blueprints/models/A3/shell_back.step

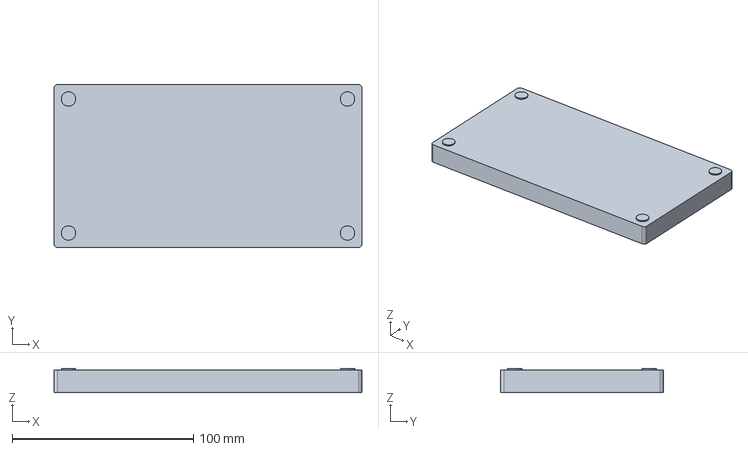
[picture p143: CAD file, 2026-09-18]
blueprints/models/A3/shell_back.step
170.0 x 90.0 x 13.3 mm
