bei22002-cpu/pocketvault-d14/blueprints/models/C11/shell_back.step

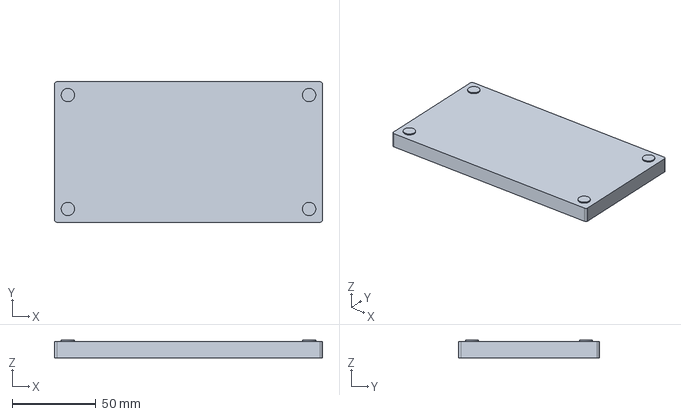
[picture p144: CAD file, 2026-09-18]
blueprints/models/C11/shell_back.step
160.0 x 84.0 x 10.7 mm
