bei22002-cpu/pocketvault-d14/blueprints/rolltop/renders/construction-diagram.png

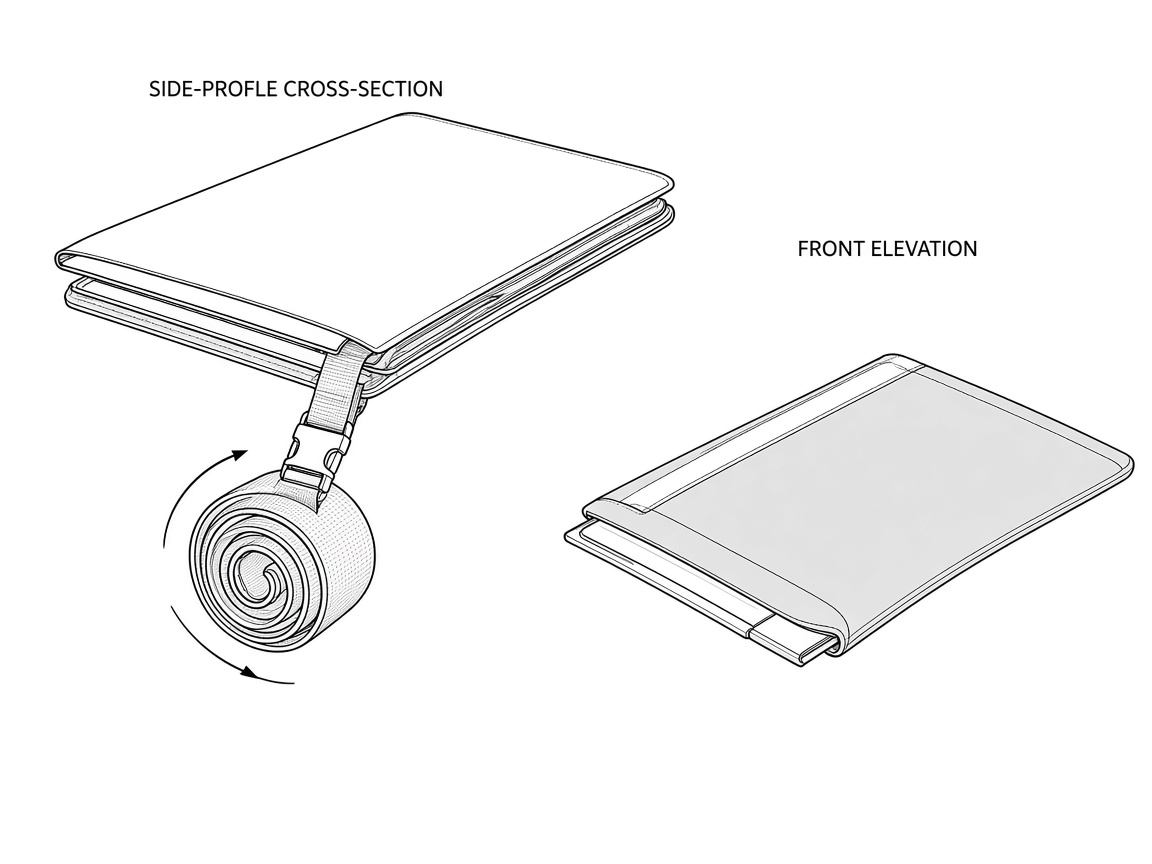
blueprints/rolltop/renders/construction-diagram.png
